brewer-michael/brwr-trmnl/firmware/src/display.cpp

#include <Arduino.h>
#include <display.h>
#include <power.h>
#include <PNGdec.h>
#include <JPEGDEC.h>
#include <Preferences.h>
#include <preferences_persistence.h>
#include <refresh_interval.h>
#include "battery_small.h"
#include "battery_hollow.h"
#include "messages.h"
#include "config.h"
#include "battery.h"
#ifdef BOARD_BRWR_TRMNL
#include <brwr/brwr.h>
#endif
#define MAX_BIT_DEPTH 8
TRMNL_DEVICE *pDevice = NULL;
#ifdef PARALLEL_EPD
#include "FastEPD.h"
FASTEPD bbep;
#else
#define BB_EPAPER
#include <bb_epaper.h>
BBEPAPER bbep;
#ifndef DEVICE_MODEL
#error "Must have a device model name defined in platformio.ini!"
#endif // DEVICE_MODEL
#include <SPIFFS.h>
#define FS SPIFFS
#endif // !PARALLEL_EPD

// List of supported TRMNL devices with SPI ePaper displays. The list can be in any order since the name is matched
// The final parameter is the panel type which is from an enumerated list
#ifdef PARALLEL_EPD
const TRMNL_DEVICE device_list[] = 
{
// name           board_name            panel_type.            sda    scl    intr   batt  batt_en batt_type
  "x",            BB_PANEL_TRMNL_X,     BB_PANEL_NONE,         0xff,  0xff,  0xff,  0xff, 0xff,   BATT_ADC,
  "m5_papers3",   BB_PANEL_M5PAPERS3,   BB_PANEL_NONE,         0xff,  0xff,  0xff,  3,    0xff,   BATT_ADC,
  "sensoria_c5",  BB_PANEL_SENSORIA_C5, BB_PANEL_NONE,         7,     6,     0,     0xff, 0xff,   BATT_ADC,
  "lilygo_t5pro", BB_PANEL_EPDIY_V7,    BBEP_DISPLAY_ED047TC1, 39,    40,    0,     0xff, 0xff,   BATT_BQ27220,
  "brwr_trmnl",   BB_PANEL_IT8951,      BBEP_DISPLAY_ED103TC2, 0xff,  0xff,  2,     PIN_BATTERY, 0xff, BATT_ADC,
  NULL, 0, 0, 0, 0, 0, 0, 0, 0,
}; // Parallel Eink device list

#else // BB_EPAPER boards
const TRMNL_DEVICE device_list[] = 
{
// name            sck   mosi   cs   rst   dc   busy  sda   scl   intr   batt  batt_en, batt_type, panel
  "og",            7,    8,     6,   10,   5,   4,    21,   20,   2,     3,    0xff,    BATT_ADC,  EPD_75,
  "og_4clr",       7,    8,     6,   10,   5,   4,    21,   20,   2,     3,    0xff,    BATT_ADC,  EPD_75_4CLR,
  "og_gen2",       6,    1,     4,   2,    5,   0,    23,   10,   3,     0xff, 0xff,    BATT_BQ27427,  EPD_75, // fake battery == 0xff
  "og_gen2_4clr",  6,    1,     4,   2,    5,   0,    11,   12,   3,     0xff, 0xff,    BATT_BQ27427,  EPD_75_4CLR, // fake battery == 0xff
  "xteink_x4",     8,    10,    21,  5,    4,   6,    0xff, 0xff, 3,     0xff, 0xff,    BATT_ADC,  EPD_426,
  "xteink_x3",     8,    10,    21,  5,    4,   6,    20,   0,    3,     0xff, 0xff,    BATT_BQ27220,  EPD_368,
  "waveshare",     13,   14,    15,  26,   27,  25,   0xff, 0xff, 33,    0xff, 0xff,    BATT_ADC,  EPD_75,
  "waveshare_397", 11,   12,    10,  46,   9,   3,    41,   42,   0,     0xff, 0xff,    BATT_AXP2101,  EPD_397,
  "seeed_sticky",  13,   14,    15,  17,   16,  18,   1,    0,    4,     0xff, 0xff,    BATT_BQ27220,  EPD_397,  
  "seeed_esp32c3", 8,    10,    3,   2,    5,   4,    0xff, 0xff, 9,     0xff, 0xff,    BATT_ADC,  EPD_75,
  "seeed_esp32s3", 7,    9,     2,   1,    4,   3,    0xff, 0xff, 0,     0xff, 0xff,    BATT_ADC,  EPD_75,
  "xiao_epaper_mini", 7, 9,     44,  38,   10,  4,    0xff, 0xff, 2,     1,    6,       BATT_ADC,  EPD_426,
  "xiao_epaper_display", 7, 9,  44,  38,   10,  4,    0xff, 0xff, 5,     1,    6,       BATT_ADC,  EPD_75,
  "xiao_epaper_3clr", 7, 9,     44,  38,   10,  4,    0xff, 0xff, 5,     1,    6,       BATT_ADC,  EPD_75_3CLR,
  "xiao_epaper_6clr", 7, 9,     44,  38,   10,  4,    0xff, 0xff, 5,     1,    6,       BATT_ADC,  EPD_75_6CLR,
  "reterminal_e1001", 7, 9,     10,  12,   11,  13,   0xff, 0xff, 3,     1,    21,      BATT_ADC,  EPD_75,
  "reterminal_e1002", 7, 9,     10,  12,   11,  13,   0xff, 0xff, 3,     1,    21,      BATT_ADC,  EPD_75_6CLR,
  "crowpanel42",   0,    0,     0,   0,    0,   0,    0xff, 0xff, 2,     0xff, 0xff,    BATT_NONE, EPD_CROWPANEL, 
#ifdef CMD_CS1_CS2
  "m5_paper_mono", 0,    0,     0,   0,    0,   0,    47,   48,   2,     0xff, 0xff,    BATT_NONE, EPD_PAPER_MONO, 
  "m5_paper_color", 0,   0,     0,   0,    0,   0,    3,    2,    1,     0xff, 0xff,    BATT_NONE, EPD_PAPER_COLOR, 
  "reterminal_e1004", 0, 0,     0,   0,    0,   0,    0xff, 0xff, 4,     1,    21,      BATT_ADC,  EPD_133_COLOR,
  "trmnl_steam",   7,    8,     6,   10,   5,   4,    21,   20,   2,     3,    0xff,    BATT_ADC,  EPD_583,
#endif
  NULL,            0,    0,     0,   0,    0,   0,    0,    0,    0,     0,    0,       0,         0,
}; // device_list

// TRMNL SPI ePaper panel types list. The list order is fixed and based on enumerated values
// N.B. ALWAYS ADD NEW PANELS TO THE END OF THE LIST
const DISPLAY_PROFILE dpList[12][3] = { // 1-bit and 2-bit display types for each profile
    {{EP75_800x480, EP75_800x480_4GRAY}, {EP75_800x480_GEN2, EP75_800x480_4GRAY_GEN2}, {EP75_800x480, EP75_800x480_4GRAY_V2}},
    {{EP426_800x480, EP426_800x480_4GRAY}, {EP426_800x480, EP426_800x480_4GRAY}, {EP426_800x480, EP426_800x480_4GRAY}},
    {{EP397_800x480, EP397_800x480_4GRAY}, {EP397_800x480, EP397_800x480_4GRAY}, {EP397_800x480, EP397_800x480_4GRAY}},
    {{EP75R_800x480, EP75R_800x480}, {EP75R_800x480, EP75R_800x480}, {EP75R_800x480, EP75R_800x480}}, 
    {{EP75YR_800x480, EP75YR_800x480}, {EP75YR_800x480, EP75YR_800x480}, {EP75YR_800x480, EP75YR_800x480}}, 
    {{EP73_SPECTRA_800x480, EP73_SPECTRA_800x480}, {EP73_SPECTRA_800x480, EP73_SPECTRA_800x480}, {EP73_SPECTRA_800x480, EP73_SPECTRA_800x480}},
    {{EPD_CROWPANEL42, EPD_CROWPANEL42_4GRAY},{EPD_CROWPANEL42, EPD_CROWPANEL42_4GRAY},{EPD_CROWPANEL42, EPD_CROWPANEL42_4GRAY}},
#ifdef CMD_CS1_CS2
    {{EP583_648x480, EP583_648x480_4GRAY}, {EP583_648x480, EP583_648x480_4GRAY}, {EP583_648x480, EP583_648x480_4GRAY}},
    {{EPD_M5_PAPER_MONO, EPD_M5_PAPER_MONO_4GRAY},{EPD_M5_PAPER_MONO, EPD_M5_PAPER_MONO_4GRAY},{EPD_M5_PAPER_MONO, EPD_M5_PAPER_MONO_4GRAY}},
    {{EPD_M5_PAPER_COLOR, EPD_M5_PAPER_COLOR},{EPD_M5_PAPER_COLOR, EPD_M5_PAPER_COLOR},{EPD_M5_PAPER_COLOR, EPD_M5_PAPER_COLOR}},
    {{EPD_SEEED_E1004, EPD_SEEED_E1004},{EPD_SEEED_E1004, EPD_SEEED_E1004},{EPD_SEEED_E1004, EPD_SEEED_E1004}},
    {{EP368_792x528, EP368_792x528_4GRAY}, {EP368_792x528, EP368_792x528_4GRAY}, {EP368_792x528, EP368_792x528_4GRAY}},
#endif
};
uint8_t u8SpectraPal[512]; // RGB333 mapped to closest Spectra6 color
#endif // !PARALLEL_EPD

#ifdef PARALLEL_EPD
#include "esp_sleep.h"
#include "driver/gpio.h"
#include "driver/rtc_io.h"
#include "LittleFS.h"
#define FS LittleFS

const uint8_t u8_graytable[] = {
/* 0 */  0, 0, 0, 0, 0, 0, 1, 1, 1, 
/* 1 */  0, 0, 1, 1, 1, 2, 2, 1, 1, 
/* 2 */  0, 0, 0, 0, 1, 2, 2, 1, 1,
/* 3 */  1, 1, 2, 2, 1, 1, 1, 1, 2, 
/* 4 */  0, 0, 0, 1, 2, 1, 1, 1, 2, 
/* 5 */  1, 2, 2, 2, 2, 1, 1, 1, 2, 
/* 6 */  0, 0, 1, 1, 2, 2, 1, 1, 2, 
/* 7 */  0, 1, 1, 2, 1, 1, 2, 1, 2, 
/* 8 */  0, 1, 1, 1, 2, 1, 2, 1, 2, 
/* 9 */  0, 1, 1, 1, 1, 2, 2, 1, 2, 
/* 10 */  1, 1, 1, 2, 1, 1, 1, 2, 2, 
/* 11 */  0, 0, 1, 2, 1, 1, 1, 2, 2, 
/* 12 */  0, 0, 0, 1, 2, 1, 1, 2, 2, 
/* 13 */  0, 0, 0, 0, 1, 2, 1, 2, 2, 
/* 14 */  0, 1, 1, 1, 2, 2, 2, 2, 2, 
/* 15 */  0, 0, 0, 0, 0, 0, 0, 0, 2
};
#include "BQ27427.h"
extern BQ27427 lipo; // Use lipo.[] to interact with the library in an Arduino 
#endif

#include "Group5.h"
#include <config.h>
#include "wifi_connect_qr.h"
#include "wifi_failed_qr.h"
#include <ctype.h> //iscntrl()
#include <api-client/display.h>
#include <inttypes.h>
#include <trmnl_log.h>
#include "png_flip.h"
#include "fonts/nicoclean_8.h"
#include "fonts/Inter_18.h"
#include "fonts/Roboto_Black_24.h"
#include <globals.h>
static uint8_t *pDither;

#ifdef BB_EPAPER
static bool display_update_epaper(int refreshMode, bool wait, bool writePlane = false, uint8_t plane = PLANE_0)
{
    if (writePlane) {
        bbep.writePlane(plane);
    }
    if (refreshMode == REFRESH_PARTIAL && !bCanDoPartial) {
        refreshMode = REFRESH_FAST;
        Log_info("Can't do partial refresh, no previous image");
    } else {
        Log_info("Have valid previous image in EPD memory, doing partial refresh");
    }
    bbep.refresh(refreshMode, wait);
    // The next update can be a partial update because the current is 1-bpp and stays in the EPD RAM
    bCanDoPartial = (bbep.getPanelType() == dpList[pDevice->panel_set][iTempProfile].OneBit);
    return true;
}

static void WriteSPIByte(uint8_t data)
{
  for (int i=0; i<8; i++) {
    digitalWrite(pDevice->epd_mosi_pin, (data & 0x80) ? 1:0);
    digitalWrite(pDevice->epd_sck_pin, 1);
    digitalWrite(pDevice->epd_sck_pin, 0);
    data <<= 1;
  }
}

static uint8_t ReadSPIByte(void)
{
uint8_t u8 = 0;
  for (int i=0; i<8; i++) {
    digitalWrite(pDevice->epd_sck_pin, 1);
    digitalWrite(pDevice->epd_sck_pin, 0);
    u8 <<= 1;
    u8 |= digitalRead(pDevice->epd_mosi_pin);
  }
return u8;
}
/**
 * @brief Function to read the EPD revision to know what temperature profile to use
 * @param none
 * @return 32-bit value read from the panel's revision (REV) command
 */
uint32_t get_panel_rev(void)
{
    uint32_t u32 = 0;
    uint8_t u8;

    if (pDevice->epd_mosi_pin == 0 && pDevice->epd_sck_pin == 0) { // pre-defined PCB+display in bb_epaper; pins unknown
        return 0;
    }
    if (pDevice->panel_set != EPD_75) { // REV (0x70) is only known to be a harmless read on the 7.5" B/W UC8179
        return 0;
    }

    // Initialize the SPI bus in 'bit-bang' mode before running the normal init sequence
    // This will allow us to use MOSI as a bidirectional line for reading data from the panel
    pinMode(pDevice->epd_sck_pin, OUTPUT);
    pinMode(pDevice->epd_cs_pin, OUTPUT);
    digitalWrite(pDevice->epd_cs_pin, 1);
    pinMode(pDevice->epd_rst_pin, OUTPUT);
    pinMode(pDevice->epd_dc_pin, OUTPUT);
    pinMode(pDevice->epd_busy_pin, INPUT);

    // Reset the panel
    digitalWrite(pDevice->epd_rst_pin, 0);
    delay(20);
    digitalWrite(pDevice->epd_rst_pin, 1);
    delay(20);
    if (digitalRead(pDevice->epd_busy_pin) == 0) { // it's a SSD16xx; not useful at the moment because our 7.5" B/W is a UC81xx type panel
        return 0;
    }
    digitalWrite(pDevice->epd_dc_pin, 0); // command mode
    digitalWrite(pDevice->epd_cs_pin, 0);
    pinMode(pDevice->epd_mosi_pin, OUTPUT);
    WriteSPIByte(0x70); // Revision (REV) command
    digitalWrite(pDevice->epd_dc_pin, 1); // data mode
    pinMode(pDevice->epd_mosi_pin, INPUT);
    for (int i=0; i<7; i++) {
        u8 = ReadSPIByte();
        if (i >= 3) { // first 3 bytes are 0xff
            u32 <<= 8;
            u32 |= u8;
        }
    }
    digitalWrite(pDevice->epd_cs_pin, 1);
    return u32;
} /* get_panel_rev() */
#endif // BB_EPAPER

String display_panel_rev_string(void)
{
    if (panel_rev == 0) {
        return String();
    }
    char sz[9];
    snprintf(sz, sizeof(sz), "%08" PRIx32, panel_rev);
    return String(sz);
} /* display_panel_rev_string() */

void hw_config_init(void)
{
    int i = 0;
    // Match the device name with the configuration in the list
    while (device_list[i].device_name && strcmp(device_list[i].device_name, DEVICE_MODEL) != 0) {
        i++;
    }
    if (device_list[i].device_name) {
        Log_info("Found device model at index %d\n", i);
        pDevice = (TRMNL_DEVICE *)&device_list[i];
    } else {
        Log_info("Device name (%s) not found in supported list!", device_list[i].device_name);
    }
} /* hw_config_init() */

/**
 * @brief Function to init the display
 * @param none
 * @return none
 */
void display_init(void)
{
    if (pDevice == NULL) {
        hw_config_init();
    }
    Log_info("dev module start");
    iTempProfile = preferences.getUInt(PREFERENCES_TEMP_PROFILE, TEMP_PROFILE_DEFAULT);
    Log_info("Saved temperature profile: %" PRIu32, iTempProfile);
#ifdef BB_EPAPER
    Log_info("BB e-Paper init");
#ifdef BOARD_SEEED_STICKY
// Special case for the Sticky - it shares the SPI bus with the uSD card, so the EPD CS line
// must be the only one active at a time
    pinMode(8, OUTPUT); // SD card CS (shared SPI with EPD)
    digitalWrite(8, 1); // SD CS disabled
    pinMode(47, OUTPUT);
    digitalWrite(47, 1); // enable EPD power
    pinMode(10, OUTPUT); // SD card enable (if it's powered down, the SPI bus may be blocked)
    digitalWrite(10, 1);
#endif // BOARD_SEEED_STICKY
    // Read the panel ID after any board-specific power/CS setup, but before bb_epaper takes over the SPI pins
    panel_rev = get_panel_rev();
    Log_info("Panel ID = 0x%08x\n", panel_rev);
    if (pDevice->epd_mosi_pin != 0 || pDevice->epd_sck_pin != 0) {
        bbep.setPanelType(dpList[pDevice->panel_set][iTempProfile].OneBit); // must be set BEFORE calling initio
        bbep.initIO(pDevice->epd_dc_pin, pDevice->epd_rst_pin, pDevice->epd_busy_pin, pDevice->epd_cs_pin,
        pDevice->epd_mosi_pin, pDevice->epd_sck_pin, 8000000);
    } else { // it's a pre-defined PCB+display in bb_epaper
        bbep.begin(dpList[pDevice->panel_set][0].OneBit);
    }
#else // Parallel eink devices
#if defined (BOARD_SEEED_RETERMINAL_E1003) || defined(BOARD_BRWR_TRMNL)
    bbep.initIT8951(EPD_MOSI_PIN, EPD_MISO_PIN, EPD_SCK_PIN, EPD_CS_PIN, EPD_BUSY_PIN, EPD_RST_PIN, EPD_EN_PIN, EPD_VCC_EN);
    bbep.setPanelSize(BBEP_DISPLAY_ED103TC2);
#ifdef BOARD_BRWR_TRMNL
    brwr::panel_after_init(); // this panel's VCOM, SPI clock for hand wiring
#endif
#else // normal parallel eink devices
    bbep.initPanel(pDevice->iBoardType);
    if (pDevice->iPanelSize != BB_PANEL_NONE) {
        bbep.setPanelSize(pDevice->iPanelSize);
    }
#endif
#ifdef BOARD_TRMNL_X
//    bbep.initPanel(BB_PANEL_TRMNL_X);
    bbep.setPasses(3, 3); // The 10.3" panel needs fewer pushes
#endif
//#elif defined( BOARD_TRMNL_X_SENSORIAS3 )
//    bbep.initPanel(BB_PANEL_V7_RAW);
//    bbep.setPanelSize(1280, 720, BB_PANEL_FLAG_MIRROR_X, -1600);
//#elif defined( BOARD_TRMNL_X_SENSORIAC5 )
//    bbep.initPanel(BB_PANEL_SENSORIA_C5);
//#elif defined(BOARD_TRMNL_X_PAPERS3)
//    bbep.initPanel(BB_PANEL_M5PAPERS3);
//#elif defined(BOARD_TRMNL_X_LILYGO)
//    bbep.initPanel(BB_PANEL_EPDIY_V7);
//    bbep.setPanelSize(960, 540);
#endif // bb_epaper
    Log_info("dev module end");
}

#ifdef BOARD_TRMNL_X

#define TCA9535_INT 38

void BQ27427_reset()
{
    bbep.ioPinMode(10, OUTPUT);

    bbep.ioWrite(10, LOW);
    delay(10);

    bbep.ioWrite(10, HIGH);
    Serial.println("BQ27427 reset performed");
}

void config_tca95535_pins_for_lp()
{
    bbep.ioPinMode(0, INPUT);

    // Pin 1 (OTG) is configured separately in init_otg()

    bbep.ioPinMode(2, INPUT);

    bbep.ioPinMode(3, INPUT);

    bbep.ioPinMode(4, INPUT);

    bbep.ioPinMode(5, INPUT);

    bbep.ioPinMode(6, OUTPUT);
    bbep.ioWrite(6, LOW);

    bbep.ioPinMode(7, INPUT);

    bbep.ioPinMode(8, OUTPUT);
    bbep.ioWrite(8, LOW);

    bbep.ioPinMode(9, OUTPUT);
    bbep.ioWrite(9, LOW);

    bbep.ioPinMode(10, INPUT);

    bbep.ioPinMode(11, OUTPUT);
    bbep.ioWrite(11, LOW);

    bbep.ioPinMode(12, OUTPUT);
    bbep.ioWrite(12, LOW);

    bbep.ioPinMode(13, OUTPUT);
    bbep.ioWrite(13, LOW);

    bbep.ioPinMode(14, INPUT);

    bbep.ioPinMode(15, INPUT);
}

void config_bma530_interrupt()
{
    bbep.ioPinMode(3, INPUT);
    bbep.ioRead(10);
}

uint8_t tca9535_interrupt_clear()
{
    return bbep.ioRead(3);
}

void otg_turn_on()
{
    bbep.ioPinMode(1, OUTPUT);
    bbep.ioWrite(1, HIGH);
    Log_info("OTG turned on");
}

void otg_turn_off()
{
    bbep.ioPinMode(1, OUTPUT);
    bbep.ioWrite(1, LOW);
    Log_info("OTG turned off");
}

#define BAT_DET_PIN       7    // TCA9535 P0_7 in bbep pin numbering
#define BAT_CHARGE_MS     2    // drive HIGH for 2 ms to charge RC network
#define BAT_TIMEOUT_US    6000 // no battery if pin is still HIGH after this
#define BAT_THRESHOLD_US  750 // >750 µs → 1 cell; ≤750 µs → 2 cells

static battery_count_t measure_battery_once()
{
    // -- Charge RC network: drive P0_7 HIGH for 2 ms --
    bbep.ioPinMode(BAT_DET_PIN, OUTPUT);
    bbep.ioWrite(BAT_DET_PIN, HIGH);
    delay(BAT_CHARGE_MS);

    // -- Release: switch to input and start timing --
    bbep.ioPinMode(BAT_DET_PIN, INPUT);

    unsigned long start = micros();
    unsigned long now   = start;
    bool timeout = false;

    while (true) {
        bool still_high = (bbep.ioRead(BAT_DET_PIN) != 0);
        now = micros();

        if (!still_high) break;               // pin went LOW → discharged

        if ((now - start) >= BAT_TIMEOUT_US) {
            timeout = true;
            break;
        }
    }

    if (timeout)                         return BATTERY_NONE;
    if ((now - start) > BAT_THRESHOLD_US) return BATTERY_ONE;
    return BATTERY_TWO;
}

battery_count_t detect_battery_count()
{
    battery_count_t last = (battery_count_t)-1;

    for (int attempt = 0; attempt < 20; attempt++) {
        battery_count_t result = measure_battery_once();

        if (result == last) {
            // Two identical results in a row — confident reading
            Log_info("Battery detection: %s (confirmed after %d attempt(s))",
                result == BATTERY_NONE ? "none" :
                result == BATTERY_ONE  ? "1 cell" : "2 cells",
                attempt + 1);
            return result;
        }

        last = result;
        delay(10);
    }

    // Fallback: return last reading if we never got two in a row
    Log_error("Battery detection: unstable reading — defaulting to last result");
    return last;
}

void enter_shipment_sleep()
{
    config_tca95535_pins_for_lp();
    bbep.ioPinMode(0, INPUT);  // Pin 0 = charger detect

    // Clear any pending TCA9535 interrupts
    for (uint8_t pin = 0; pin < 16; pin++) {
        bbep.ioPinMode(pin, INPUT);
        bbep.ioRead(pin);
    }
    delay(50);

    pinMode(TCA9535_INT, INPUT_PULLUP);

    // Check initial GPIO38 state
    int gpio38_state = digitalRead(TCA9535_INT);

    // Enable GPIO wakeup for light sleep
    esp_err_t err = esp_sleep_enable_gpio_wakeup();
    if (err != ESP_OK) {
        Serial.printf("ERROR: Failed to enable GPIO wakeup: %d\n", err);
        return;
    }

    err = gpio_wakeup_enable((gpio_num_t)TCA9535_INT, GPIO_INTR_LOW_LEVEL);
    if (err != ESP_OK) {
        Serial.printf("ERROR: Failed to configure GPIO38 wakeup: %d\n", err);
        return;
    }

    Serial.println("=== Entering shipment mode light sleep loop ===");
    delay(100);

    uint32_t sleep_count = 0;

    // Main sleep loop
    while (true) {
        sleep_count++;

        esp_light_sleep_start();

        // Re-initialize Serial after light sleep (USB may have been disabled)
        delay(100);
        Serial.begin(115200);
        delay(100);

        Serial.println("\n=== WAKEUP from light sleep ===");
        Serial.printf("Sleep cycle: %lu\n", sleep_count);

        // Check wakeup cause
        esp_sleep_wakeup_cause_t wakeup_reason = esp_sleep_get_wakeup_cause();
        Serial.printf("Wakeup cause: %d (GPIO=%d)\n", wakeup_reason, ESP_SLEEP_WAKEUP_GPIO);

        if (wakeup_reason == ESP_SLEEP_WAKEUP_GPIO) {
            Serial.println("GPIO wakeup detected");

            // Check GPIO38 state
            gpio38_state = digitalRead(TCA9535_INT);
            Serial.printf("GPIO38 state after wakeup: %d\n", gpio38_state);

            // Check if charger connected (TCA9535 pin 0 LOW)
            bbep.ioPinMode(0, INPUT);
            delay(10);
            uint8_t pin0_state = bbep.ioRead(0);
            Serial.printf("TCA9535 pin 0 (charger detect): %d (0=charger present)\n", pin0_state);

            if (pin0_state == 0) {
                Serial.println("*** CHARGER DETECTED - Exiting shipment mode ***");
                Serial.flush();
                delay(100);
                break;  // Exit shipment mode
            }

            // False wakeup - clear interrupt and continue
            for (uint8_t pin = 0; pin < 16; pin++) {
                bbep.ioPinMode(pin, INPUT);
                bbep.ioRead(pin);
            }
            delay(50);

            gpio38_state = digitalRead(TCA9535_INT);
            Serial.printf("GPIO38 after clear: %d\n", gpio38_state);

        } else {
            Serial.printf("Unexpected wakeup cause: %d\n", wakeup_reason);
        }

        Serial.println("Returning to sleep...\n");
        Serial.flush();
        delay(100);
    }

    gpio_wakeup_disable((gpio_num_t)TCA9535_INT);
    gpio_set_intr_type((gpio_num_t)TCA9535_INT, GPIO_INTR_DISABLE);
    Serial.println("=== Exited shipment mode successfully ===");
    Serial.flush();
}

#define PIN_ESP32C5_SPI_BOOT 4
#define PIN_ESP32C5_USB_BOOT 5
#define PIN_ESP32C5_EN 6

void modem_enter_bootloader(void) {
  // Disable target and wait for full power down
  bbep.ioWrite(PIN_ESP32C5_EN, 0);
  delay(100);

  // Configure boot pins for bootloader mode
  bbep.ioPinMode(PIN_ESP32C5_SPI_BOOT, OUTPUT);
  bbep.ioPinMode(PIN_ESP32C5_USB_BOOT, OUTPUT);
  bbep.ioWrite(PIN_ESP32C5_SPI_BOOT, 0);
  bbep.ioWrite(PIN_ESP32C5_USB_BOOT, 1);
  delay(50);

  // Enable target in bootloader mode
  bbep.ioWrite(PIN_ESP32C5_EN, 1);
  delay(300);
}

void modem_reset_target(void) {
  // Disable target
  bbep.ioWrite(PIN_ESP32C5_EN, 0);
  delay(50);

  // Release boot pins (set to input for normal boot)
  bbep.ioPinMode(PIN_ESP32C5_SPI_BOOT, INPUT);
  bbep.ioPinMode(PIN_ESP32C5_USB_BOOT, INPUT);
  delay(50);

  // Enable target (normal boot)
  bbep.ioWrite(PIN_ESP32C5_EN, 1);
}

#endif

/**
 * @brief Enable or disable light sleep at runtime
 * @param enabled true to enable light sleep, false to disable
 * @return none
 */
void display_set_light_sleep(uint8_t enabled)
{
#ifdef BB_EPAPER
    bbep.setLightSleep(enabled);
#endif
}

// Clear any ghosting on the X display by wiping it black/white many times
void display_wipe(void)
{
#ifdef BB_EPAPER

#ifdef BOARD_TRMNL_4CLR
    int refreshCount = 2;
#else
    int refreshCount = 60;
#endif

    bbep.setPanelType(dpList[pDevice->panel_set][iTempProfile].OneBit);
    bbep.fillScreen(BBEP_WHITE);
    for (int i=0; i<refreshCount; i++) {
        bbep.refresh(REFRESH_FULL); // 2 to 3 minutes of Black/White clearing of the display
    }
    bbep.sleep(LIGHT_SLEEP);
#else
    bbep.setMode(BB_MODE_1BPP);
    bbep.fillScreen(BBEP_WHITE);
    for (int i=0; i<100; i++) { // 200 black/white cycles should remove any ghosting
        bbep.fullUpdate(CLEAR_SLOW, true);
    }
    bbep.einkPower(0); // power off the display
#endif
} /* display_wipe() */

/**
 * @brief Function to sleep the ESP32 while saving power
 * @param u32Millis represents the sleep time in milliseconds
 * @return none
 */
void display_sleep(uint32_t u32Millis)
{
#ifdef DO_NOT_LIGHT_SLEEP
    delay(u32Millis);
#else
    // Runtime control for light sleep (true = enabled, false = disabled)
    static bool light_sleep_enabled = true;
    if (!light_sleep_enabled) {
        delay(u32Millis);
    } else {
        esp_sleep_enable_timer_wakeup(u32Millis * 1000L);
        esp_light_sleep_start();
    }
#endif
}

/**
 * @brief Function to reset the display
 * @param none
 * @return none
 */
void display_reset(void)
{
    Log_info("e-Paper Clear start");
    bbep.fillScreen(BBEP_WHITE);
#ifdef BB_EPAPER
#ifndef BOARD_SEEED_RETERMINAL_E1002
    bbep.setLightSleep(true);
#endif
    if (!display_update_epaper(apiDisplayResult.response.maximum_compatibility ? REFRESH_FULL : REFRESH_FAST, true)) {
        Log_error("display_reset: e-paper update failed");
    }
#else
    bbep.fullUpdate();
#endif
    Log_info("e-Paper Clear end");
    // DEV_Delay_ms(500);
}

/**
 * @brief Function to read the display height
 * @return uint16_t - height of display in pixels
 */
uint16_t display_height()
{
    return bbep.height();
}

/**
 * @brief Function to read the display width
 * @return uint16_t - width of display in pixels
 */
uint16_t display_width()
{
    return bbep.width();
}

#ifdef PARALLEL_EPD
void display_draw_touchbar_indicator(touchbar_side_t side, bool filled)
{
    const int radius = 24;
    const int margin_bottom = 20;
    int w = bbep.width();
    int h = bbep.height();
    int x;
    Log_info("Drawing touchbar indicator %d\n", (int)side);
    switch (side) {
        case TOUCHBAR_LEFT:   x = w / 6;     break;
        case TOUCHBAR_MIDDLE: x = w / 2;     break;
        case TOUCHBAR_RIGHT:  x = w * 5 / 6; break;
        default: return;
    }
    int y = h - margin_bottom - radius;
    int prev_mode = bbep.getPreviousMode();
        const int rect_h = radius * 2;
        const int rect_w = rect_h * 4;
        const int border = 3;
        int rx = x - rect_w / 2;
        int ry = y - rect_h / 2;
        uint8_t fill_color   = filled ? BBEP_BLACK : BBEP_WHITE;
        uint8_t border_color = filled ? BBEP_WHITE : BBEP_BLACK;
        if (prev_mode == BB_MODE_NONE) {
            bbep.setMode(BB_MODE_1BPP);
            // No previous image, so in order to get what we need in a partial update, we need to
            // set the colors to the opposite of what we want drawn.
            bbep.fillScreen(BBEP_WHITE);
            bbep.drawRect(rx - border - 1, ry - border - 1, rect_w + 2 + (2*border), rect_h + 2 + (2*border), border_color);
            bbep.fillRect(rx - border, ry - border, rect_w + (2*border), rect_h + (2*border), fill_color);
            bbep.fillRect(rx, ry, rect_w, rect_h, border_color);
            int sz = bbep.width() * bbep.height() / 8; // 1-bit per pixel
            memcpy(bbep.previousBuffer(), bbep.currentBuffer(), sz);
            bbep.setPreviousMode(BB_MODE_1BPP);
        }
        // Draw outline, then larger filled rect for border color and inner for fill color
        bbep.drawRect(rx - border - 1, ry - border - 1, rect_w + 2 + (2*border), rect_h + 2 + (2*border), fill_color);
        bbep.fillRect(rx - border, ry - border, rect_w + (2*border), rect_h + (2*border), border_color);
        bbep.fillRect(rx, ry, rect_w, rect_h, fill_color);
        bbep.partialUpdate(false);
} /* display_draw_touchbar_indicator() */
#endif

/**
 * @brief Function to draw multi-line text onto the display
 * @param x_start X coordinate to start drawing
 * @param y_start Y coordinate to start drawing
 * @param message Text message to draw
 * @param max_width Maximum width in pixels for each line
 * @param font_width Width of a single character in pixels
 * @param color_fg Foreground color
 * @param color_bg Background color
 * @param font Font to use
 * @param is_center_aligned If true, center the text; if false, left-align
 * @return none
 */
void Paint_DrawMultilineText(UWORD x_start, UWORD y_start, const char *message,
                             uint16_t max_width, uint16_t font_width,
                             UWORD color_fg, UWORD color_bg, const void *font,
                             bool is_center_aligned)
{
    BB_FONT_SMALL *pFont = (BB_FONT_SMALL *)font;
    uint16_t display_width_pixels = max_width;
    int max_chars_per_line = display_width_pixels / font_width;
    const int font_height = pFont->height;
    uint8_t MAX_LINES = 4;

    char lines[MAX_LINES][max_chars_per_line + 1] = {0};
    uint16_t line_count = 0;

    int text_len = strlen(message);
    int current_width = 0;
    int line_index = 0;
    int line_pos = 0;
    int word_start = 0;
    int i = 0;
    char word_buffer[max_chars_per_line + 1] = {0};
    int word_length = 0;

    bbep.setFont(font);
    bbep.setTextColor(color_fg, color_bg);

    bbep.setFont(font);
    bbep.setTextColor(color_fg, color_bg);

    while (i <= text_len && line_index < MAX_LINES)
    {
        word_length = 0;
        word_start = i;

        // Skip leading spaces
        while (i < text_len && message[i] == ' ')
        {
            i++;
        }
        word_start = i;

        // Find end of word or end of text
        while (i < text_len && message[i] != ' ')
        {
            i++;
        }

        word_length = i - word_start;
        if (word_length > max_chars_per_line)
        {
            word_length = max_chars_per_line; // Truncate if word is too long
        }

        if (word_length > 0)
        {
            strncpy(word_buffer, message + word_start, word_length);
            word_buffer[word_length] = '\0';
        }
        else
        {
            i++;
            continue;
        }

        int word_width = word_length * font_width;

        // Check if adding the word exceeds max_width
        if (current_width + word_width + (current_width > 0 ? font_width : 0) <= display_width_pixels)
        {
            // Add space before word if not the first word in the line
            if (current_width > 0 && line_pos < max_chars_per_line - 1)
            {
                lines[line_index][line_pos++] = ' ';
                current_width += font_width;
            }

            // Add word to current line
            if (line_pos + word_length <= max_chars_per_line)
            {
                strcpy(&lines[line_index][line_pos], word_buffer);
                line_pos += word_length;
                current_width += word_width;
            }
        }
        else
        {
            // Current line is full, draw it
            if (line_pos > 0)
            {
                lines[line_index][line_pos] = '\0'; // Null-terminate the current line
                line_index++;
                line_count++;

                if (line_index >= MAX_LINES)
                {
                    break;
                }

                // Start new line with this word
                strncpy(lines[line_index], word_buffer, word_length);
                line_pos = word_length;
                current_width = word_width;
            }
            else
            {
                // Single long word case
                strncpy(lines[line_index], word_buffer, max_chars_per_line);
                lines[line_index][max_chars_per_line] = '\0';
                line_index++;
                line_count++;
                line_pos = 0;
                current_width = 0;
            }
        }

        // Move to next word
        if (message[i] == ' ')
        {
            i++;
        }
    }

    // Store the last line if any
    if (line_pos > 0 && line_index < MAX_LINES)
    {
        lines[line_index][line_pos] = '\0';
        line_count++;
    }

    // Draw the lines
    for (int j = 0; j < line_count; j++)
    {
        uint16_t line_width = strlen(lines[j]) * font_width;
        uint16_t draw_x = x_start;

        if (is_center_aligned)
        {
            if (line_width < max_width)
            {
                draw_x = x_start + (max_width - line_width) / 2;
            }
        }
        bbep.setCursor(draw_x, y_start + j * (font_height + 5));
        bbep.print(lines[j]);
    }
}
/**
 * @brief Reduce the bit depth of line of pixels using thresholding (aka simple color mapping)
 * @param Destination bit count (1 or 2)
 * @param Pointer to a PNG palette (3 bytes per entry)
 * @param Pointer to the source pixels
 * @param Pointer to the destination pixels
 * @param Pixel count
 * @param Original bit depth
 * @return none
 */
void ReduceBpp(int iDestBpp, int iPixelType, uint8_t *pPalette, uint8_t *pSrc, uint8_t *pDest, int w, int iSrcBpp)
{
    int g = 0, x, iDelta;
    uint8_t *s, *d, *pPal, u8, count;
    const uint8_t u8G2ToG8[4] = {0x00, 0x55, 0xaa, 0xff}; // 2-bit to 8-bit gray

    if (iPixelType == PNG_PIXEL_TRUECOLOR) iSrcBpp = 24;
    else if (iPixelType == PNG_PIXEL_TRUECOLOR_ALPHA) iSrcBpp = 32;
    iDelta = iSrcBpp/8; // bytes per pixel
    count = 8; // bits in a byte
    u8 = 0; // start with all black
    d = pDest;
    s = pSrc;
    for (x=0; x<w; x++) {
        u8 <<= iDestBpp;
        switch (iSrcBpp) {
            case 24:
            case 32:
                g = (s[0] + s[1]*2 + s[2])/4; // convert color to gray value
                s += iDelta;
                break;
            case 8:
                if (iPixelType == PNG_PIXEL_INDEXED) {
                    pPal = &pPalette[s[0] * 3];
                    g = (pPal[0] + pPal[1]*2 + pPal[2])/4;
                } else { // must be grayscale
                    g = s[0];
                }
                s++;
                break;
            case 4:
                if (x & 1) {
                    if (iPixelType == PNG_PIXEL_INDEXED) {
                        pPal = &pPalette[(s[0] & 0xf) * 3];
                        g = (pPal[0] + pPal[1]*2 + pPal[2])/4;
                    } else {
                        g = (s[0] & 0xf) | (s[0] << 4);
                    }
                    s++;
                } else {
                    if (iPixelType == PNG_PIXEL_INDEXED) {
                        pPal = &pPalette[(s[0]>>4) * 3];
                        g = (pPal[0] + pPal[1]*2 + pPal[2])/4;
                    } else {
                        g = (s[0] & 0xf0) | (s[0] >> 4);
                    }
                }
                break;
            case 2: // We need to handle this case for 2-bit images with (random) palettes
                g = s[0] >> (6-((x & 3) * 2));
                if (iPixelType == PNG_PIXEL_INDEXED) {
                    pPal = &pPalette[(g & 3)*3];
                    g = (pPal[0] + pPal[1]*2 + pPal[2])/4;
                } else {
                    g = u8G2ToG8[g & 3];
                }
                if ((x & 3) == 3) {
                    s++;
                }
                break;
        } // switch on bpp
        if (iDestBpp == 1) {
            u8 |= (g >> 7); // B/W
        } else if (iDestBpp == 2) { // generate 4 gray levels (2 bits)
            u8 |= (3 ^ (g >> 6)); // 4 gray levels (inverted relative to 1-bit)
        } else { // must be 4-bpp output
            u8 |= (g >> 4);
        }
        count -= iDestBpp;
        if (count == 0) { // byte is full, move on
            *d++ = u8;
            u8 = 0;
            count = 8;
        }
    } // for x
    if (count != 8) { // partial byte remaining
        u8 <<= count;
        *d++ = u8;
    }
} /* ReduceBpp() */
enum {
    PNG_1_BIT = 0,
    PNG_1_BIT_INVERTED,
    PNG_2_BIT_0,
    PNG_2_BIT_1,
    PNG_2_BIT_BOTH,
    PNG_2_BIT_INVERTED,
};
#ifdef BB_EPAPER
//
// Match the given pixel to black (00), white (01), or red (1x)
//
unsigned char GetBWRPixel(int r, int g, int b)
{
    uint8_t ucOut=BBEP_BLACK;
    int gr;

    gr = (b + r + g*2)>>2; // gray
    // match the color to closest of black/white/red
    if (r > g && r > b) { // red is dominant
        if (gr < 100 && r < 80) {
            // black
        } else {
            if (r-b > 32 && r-g > 32) {
                // is red really dominant?
                ucOut = BBEP_RED; // red (can be 2 or 3, but 3 is compatible w/BWYR)
            } else { // yellowish should be white
                // no, use white instead of pink/yellow
                ucOut = BBEP_WHITE;
            }
        }
    } else { // check for white/black
        if (gr >= 128) {
            ucOut = BBEP_WHITE; // white
        } else {
            // black
        }
    }
    return ucOut;
} /* GetBWRPixel() */
//
// Match the given pixel to black (00), white (01), yellow (10), or red (11)
// returns 2 bit value of closest matching color
//
unsigned char GetBWYRPixel(int r, int g, int b)
{
    uint8_t ucOut=BBEP_BLACK;
    int gr;

    gr = (b + r + g*2)>>2; // gray
    // match the color to closest of black/white/yellow/red
    if (r > b || g > b) { // red or yellow is dominant
        if (gr < 90 && r < 80 && g < 80) {
            // black
        } else {
            if (r-b > 32 && r-g > r/2) {
                // is red really dominant?
                ucOut = BBEP_RED; // red
            } else if (r-b > 32 && g-b > 32) {
                // yes, yellow
                ucOut = BBEP_YELLOW;
            } else {
                ucOut = BBEP_WHITE; // gray/white
            }
        }
    } else { // check for white/black
        if (gr >= 100) {
            ucOut = BBEP_WHITE; // white
        } else {
            // black
        }
    }
    return ucOut;
} /* GetBWYRPixel() */

//
// bb_epaper colors to map to Spectra6 colors
// The RGB values are not correct for the panel, but for simple mapping
// these work best. These get mapped from bb_epaper color indices to
// Spectra6 color indices by the setPixel() method.
//
const int iSpectraRGB[] = { // r, g, b
    0, 0, 0, // black = 0
    192,192,192, // white = 1
    192,192,0, // yellow = 2
    192,0,0, // red = 3
    0,0,192, // blue = 4
    0,192,0, // green = 5
};
// Map the Spectra6 palette to the closest RGB333 values
void CreateSpectra6Pal(void)
{
    int i, j;
    int r, g, b, r1, g1, b1;
    int dist, min_dist, min_index;

    for (i=0; i<512; i++) { // RGB333
        r = (i & 7)*36;
        g = ((i >> 3) & 7)*36;
        b = (i >> 6)*36;
        min_dist = 0x7fffffff;
        min_index = 0;
        for (j=0; j<6; j++) { // match to the closes Spectra6 color
            r1 = iSpectraRGB[j*3];
            g1 = iSpectraRGB[j*3+1];
            b1 = iSpectraRGB[j*3+2];
            dist = (r - r1) * (r - r1); // delta red squared
            dist += (g - g1) * (g - g1); // delta green squared
            dist += (b - b1) * (b - b1); // delta blue squared
            if (dist < min_dist) {
                min_dist = dist;
                min_index = j;
            }
        } // for j
        u8SpectraPal[i] = min_index; // best match palette index for this RGB333 color
    } // for i
} /* CreateSpectra6Pal() */
//
// Convert the RGB value into one of 6 Spectra6 colors
//
uint8_t GetSpectraPixel(int r, int g, int b)
{
uint8_t c;
uint16_t rgb333;

    rgb333 = (r>>5) + ((g & 0xe0) >> 2) + ((b & 0xe0) << 1);
    c = u8SpectraPal[rgb333];
    return c;
} /* GetSpectraPixel() */

/**
 * @brief Callback function for each line of PNG decoded
 * @param PNGDRAW structure containing the current line and relevant info
 * @return none
 */
//
// Draw the PNG image into the local framebuffer memory using the drawPixel() method
// to do color translation and to properly format the memory layout
//
int png_draw_6clr(PNGDRAW *pDraw)
{
    uint8_t r=0, g=0, b=0, *s, *pPal, *pPalette = pDraw->pPalette;
    int x, y, iDelta, iBpp = pDraw->iBpp;
    y = pDraw->y;
    switch (pDraw->iPixelType) {
        case PNG_PIXEL_INDEXED:
            break;
        case PNG_PIXEL_TRUECOLOR:
	        if (iBpp <= 8) {
                iBpp *= 3;
	        }
            pPalette = NULL;
            break;
        case PNG_PIXEL_TRUECOLOR_ALPHA:
	        if (iBpp <= 8) {
                iBpp *= 4;
	        }
            pPalette = NULL;
            break;
        case PNG_PIXEL_GRAYSCALE:
            pPalette = NULL;
            break;
    } // switch on pixel type
    iDelta = iBpp/8;
    s = pDraw->pPixels;
    for (x=0; x<pDraw->iWidth; x++) { // slower code, but less code :)
        switch (iBpp) {
            case 24:
            case 32:
                r = s[0];
                g = s[1];
                b = s[2];
                s += iDelta;
                break;
            case 16:
                r = s[1] & 0xf8; // red
                g = ((s[0] | s[1] << 8) >> 3) & 0xfc; // green
                b = s[0] << 3;
                s += 2;
                break;
                case 8:
                    if (pPalette) {
                        pPal = &pPalette[s[0] * 3];
                        r = pPal[0];
                        g = pPal[1];
                        b = pPal[2];
                    } else {
                        r = g = b = s[0];
                    }
                    s++;
                    break;
                case 4:
                    if (pPalette) {
                        if (x & 1) {
                            pPal = &pPalette[(s[0] & 0xf) * 3];
                            s++;
                        } else {
                            pPal = &pPalette[(s[0]>>4) * 3];
                        }
                        r = pPal[0];
                        g = pPal[1];
                        b = pPal[2];
                    } else {
                        if (x & 1) {
                            r = g = b = (s[0] & 0xf) | (s[0] << 4);
                            s++;
                        } else {
                            r = g = b = (s[0] >> 4) | (s[0] & 0xf0);
                        }
                    }
                    break;
		case 2:
		    if (pPalette) {
			pPal = &pPalette[((s[0] >> ((3-(x&3))*2)) & 3) * 3];
			r = pPal[0]; g = pPal[1]; b = pPal[2];
		    } else {
			r = g = b = (s[0] << ((x&3)*2)) & 0xc0;
		    }
		    if ((x & 3) == 3) s++;
		    break;
                case 1:
                    if (pPalette) {
                        pPal = &pPalette[((s[0] >> (7-(x&7))) & 1) * 3];
                        r = pPal[0]; g = pPal[1]; b = pPal[2];
                    } else {
                        r = g = b = ((s[0] << (x&7)) & 0x80);
                    }
                    if ((x & 7) == 7) s++;
                    break;
            } // switch on bpp
            bbep.drawPixel(x, y, GetSpectraPixel(r, g, b));
        } // for x
    return 1; // continue decoding
} /* png_draw_6clr() */

#ifdef BOARD_TRMNL_4CLR
//
// Draw the PNG image into the local framebuffer memory using the drawPixel() method
// to do color translation and to properly format the memory layout
//
int png_draw_4clr(PNGDRAW *pDraw)
{
    uint8_t r=0, g=0, b=0, *s, *pPal, *pPalette = pDraw->pPalette;
    int x, iDelta, iBpp = pDraw->iBpp;
    uint8_t uc=0, *d, *pTemp = bbep.getCache(); // get some scratch memory (not from the stack)

    d = pTemp;
    switch (pDraw->iPixelType) {
        case PNG_PIXEL_INDEXED:
            break;
        case PNG_PIXEL_TRUECOLOR:
	        if (iBpp <= 8) {
                iBpp *= 3;
	        }
            pPalette = NULL;
            break;
        case PNG_PIXEL_TRUECOLOR_ALPHA:
	        if (iBpp <= 8) {
                iBpp *= 4;
	        }
            pPalette = NULL;
            break;
        case PNG_PIXEL_GRAYSCALE:
            pPalette = NULL;
            break;
    } // switch on pixel type
    iDelta = iBpp/8;
    s = pDraw->pPixels;
    for (x=0; x<pDraw->iWidth; x++) { // slower code, but less code :)
        switch (iBpp) {
            case 24:
            case 32:
                r = s[0];
                g = s[1];
                b = s[2];
                s += iDelta;
                break;
            case 16:
                r = s[1] & 0xf8; // red
                g = ((s[0] | s[1] << 8) >> 3) & 0xfc; // green
                b = s[0] << 3;
                s += 2;
                break;
                case 8:
                    if (pPalette) {
                        pPal = &pPalette[s[0] * 3];
                        r = pPal[0];
                        g = pPal[1];
                        b = pPal[2];
                    } else {
                        r = g = b = s[0];
                    }
                    s++;
                    break;
                case 4:
                    if (pPalette) {
                        if (x & 1) {
                            pPal = &pPalette[(s[0] & 0xf) * 3];
                            s++;
                        } else {
                            pPal = &pPalette[(s[0]>>4) * 3];
                        }
                        r = pPal[0];
                        g = pPal[1];
                        b = pPal[2];
                    } else {
                        if (x & 1) {
                            r = g = b = (s[0] & 0xf) | (s[0] << 4);
                            s++;
                        } else {
                            r = g = b = (s[0] >> 4) | (s[0] & 0xf0);
                        }
                    }
                    break;
                case 2:
                    if (pPalette) {
                    pPal = &pPalette[((s[0] >> ((3-(x&3))*2)) & 3) * 3];
                    r = pPal[0]; g = pPal[1]; b = pPal[2];
                    } else {
                    r = g = b = (s[0] << ((x&3)*2)) & 0xc0;
                    }
                    if ((x & 3) == 3) s++;
                    break;
                case 1:
                    if (pPalette) {
                        pPal = &pPalette[((s[0] >> (7-(x&7))) & 1) * 3];
                        r = pPal[0]; g = pPal[1]; b = pPal[2];
                    } else {
                        r = g = b = ((s[0] << (x&7)) & 0x80);
                    }
                    if ((x & 7) == 7) s++;
                    break;
            } // switch on bpp
            uc <<= 2;
            uc |= GetBWYRPixel(r, g, b); // get the best matching 2-bit color
            if ((x & 3) == 3) { // 4 pixels packed into each byte
                *d++ = uc;
            }
        } // for x
    bbep.writeData(pTemp, (pDraw->iWidth+3)/4);
    return 1; // continue decoding
} /* png_draw4clr() */
#endif // BOARD_TRMNL_4CLR (4 color only)

int png_draw(PNGDRAW *pDraw)
{
    int x;
    uint8_t ucBppChanged = 0, ucInvert = 0;
    uint8_t uc, ucMask, src, *s, *d, *pTemp = bbep.getCache(); // get some scratch memory (not from the stack)
    int iPlane = *(int *)pDraw->pUser;
    int iWidth;

    iWidth = pDraw->iWidth;
    if (pDraw->y >= bbep.height()) return 0; // stop decoding if we'll go past the bottom
    if (iWidth > bbep.width()) iWidth = bbep.width(); // crop image width to display size if it's larger

    if (pDraw->iPixelType == PNG_PIXEL_INDEXED || pDraw->iBpp > 2) {
        if (pDraw->iBpp == 1) { // 1-bit output, just see which color is brighter
            uint32_t u32Gray0, u32Gray1;
            u32Gray0 = pDraw->pPalette[0] + (pDraw->pPalette[1]<<2) + pDraw->pPalette[2];
            u32Gray1 = pDraw->pPalette[3] + (pDraw->pPalette[4]<<2) + pDraw->pPalette[5];
          if (u32Gray0 < u32Gray1) {
            ucInvert = 0xff;
          }
        } else {
            // Reduce the source image to 1-bpp or 2-bpp
            ReduceBpp((pDraw->pUser) ? 2:1, pDraw->iPixelType, pDraw->pPalette, pDraw->pPixels, pTemp, iWidth, pDraw->iBpp);
            ucBppChanged = 1;
        }
    } else if (pDraw->iBpp == 2) {
        ucInvert = 0xff; // 2-bit non-palette images need to be inverted colors for 4-gray mode
    }
    s = (ucBppChanged) ? pTemp : (uint8_t *)pDraw->pPixels;
    d = pTemp;
    if (iPlane == PNG_1_BIT || iPlane == PNG_1_BIT_INVERTED) {
        // 1-bit output, decode the single plane and write it
        if (iPlane == PNG_1_BIT_INVERTED) ucInvert = ~ucInvert; // to do PLANE_FALSE_DIFF
        if (iPlane == PNG_1_BIT_INVERTED && (bbep.capabilities() & BBEP_3COLOR)) { // write the red plane as 0's for this case
            memset(d, 0, iWidth/8);
        } else {
            for (x=0; x<iWidth; x+= 8) {
                d[0] = s[0] ^ ucInvert;
                d++; s++;
            }
        }
    } else { // we need to split the 2-bit data into plane 0 and 1
        src = *s++;
        src ^= ucInvert;
        uc = 0; // suppress warning/error
        if (iPlane == PNG_2_BIT_BOTH || iPlane == PNG_2_BIT_INVERTED) { // draw 2bpp data as 1-bit to use for partial update
            if (iPlane == PNG_2_BIT_BOTH) {
                ucInvert = ~ucInvert; // the invert rule is backwards for grayscale data
            }
            src = ~src;
            for (x=0; x<iWidth; x++) {
                uc <<= 1;
                if (src & 0xc0) { // non-white -> black
                    uc |= 1; // high bit of source pair
                }
                src <<= 2;
                if ((x & 3) == 3) { // new input byte
                    src = *s++;
                    src ^= ucInvert;
                }
                if ((x & 7) == 7) { // new output byte
                    *d++ = uc;
                }
            } // for x
        } else { // normal 0/1 split plane
            ucMask = (iPlane == PNG_2_BIT_0) ? 0x40 : 0x80; // lower or upper source bit
            for (x=0; x<iWidth; x++) {
                uc <<= 1;
                if (src & ucMask) {
                    uc |= 1; // high bit of source pair
                }
                src <<= 2;
                if ((x & 3) == 3) { // new input byte
                    src = *s++;
                    src ^= ucInvert;
                }
                if ((x & 7) == 7) { // new output byte
                    *d++ = uc;
                }
            } // for x
        }
    }
    bbep.writeData(pTemp, (iWidth+7)/8);
    return 1;
} /* png_draw() */
#else // TRMNL_X version
// The generic 2-bit gray update procedure is too dark on the X's 10.3" panel, so
// we need to use the more complex 4-bit update method which has a custom pattern
// specifically for that panel's characteristics. This loop maps 2-bit pixels to
// 4-bit pixels by converting the values 0/1/2/3 to 0/5/10/15
static void Expand2bppLineTo4bpp(const uint8_t *src, uint8_t *dest, int width)
{
    uint8_t b;
    uint16_t u16;

    for (int x = 0; x < width; x+=4) {
        u16 = 0;
        b = *src++;
        for (int j=0; j<4; j++) {
            u16 <<= 4;
            u16 |= (((b >> 6) & 3) * 5);
            b <<= 2;
        } // for j
      *dest++ = (uint8_t)(u16 >> 8);
      *dest++ = (uint8_t)(u16 & 0xff);
    } // for x
} /* Expand2bppLineTo4bpp() */

int png_draw(PNGDRAW *pDraw)
{
    int x, y = pDraw->y;
    uint8_t uc = 0;
    uint8_t ucMask, ucPixel, src, *s, *d;
    int iPitch, iBpp;

    if (y >= bbep.height() && pDraw->iWidth != bbep.height()) return 0; // image is larger than the display (and not rotated), stop decoding it
    if (pDraw->iPixelType == PNG_PIXEL_INDEXED || pDraw->iBpp > 4) { // need to convert through the palette and/or reduce the bpp
        s = bbep.tempBuffer(); // temp space we can use
        iBpp = (pDraw->iBpp > 4) ? 4 : pDraw->iBpp;
        if (iBpp == 2) iBpp = 4; // 2-bit indexed images -> 4bpp for calibrated gray refresh
        ReduceBpp(iBpp, pDraw->iPixelType, pDraw->pPalette, pDraw->pPixels, s, pDraw->iWidth, pDraw->iBpp);
    } else { // for grayscale images of 1/2/4-bpp we can directly use the pixels as-is
        iBpp = pDraw->iBpp;
        s = (uint8_t *)pDraw->pPixels;
    }
    if (pDraw->pUser) { // drawing previous image into previous buffer
        d = bbep.previousBuffer();
        switch (iBpp) { // if this matches the new image we can do a non-flickering update
            case 1:
                bbep.setPreviousMode(BB_MODE_1BPP);
                break;
            default:
                bbep.setPreviousMode(BB_MODE_4BPP);
                break;
        }
    } else {
        d = bbep.currentBuffer();
    }
    iPitch = bbep.width()/2;
    if (iBpp == 1) {
        if (bbep.width() >= pDraw->iWidth) { // normal orientation
            iPitch = (bbep.width() + 7)/8;
            d += y * iPitch; // point to the correct line
            memcpy(d, s, (pDraw->iWidth+7)/8);
        } else { // rotated
            uint8_t ucPixel, ucMask, j;
            d += (bbep.height() - 1) * iPitch;
            d += (y / 8);
            ucMask = 0x80 >> (y & 7); // destination mask
            for (x=0; x<pDraw->iWidth; x++) {
                if ((x & 7) == 0) uc = *s++;
                ucPixel = d[0] & ~ucMask; // unset old pixel
                if (uc & 0x80) ucPixel |= ucMask;
                d[0] = ucPixel;
                uc <<= 1;
                d -= iPitch;
            }
        }
    } else {
        if (iBpp == 2) { // expand 2-bit grayscale to 4-bit for calibrated refresh
            Expand2bppLineTo4bpp(s, bbep.tempBuffer(), pDraw->iWidth);
            s = bbep.tempBuffer();
            iBpp = 4;
        }
        // 4-bit native format (includes expanded 2-bit)
        if (bbep.width() == pDraw->iWidth) { // normal orientation
            d += y * iPitch; // point to the correct line
            memcpy(d, s, (pDraw->iWidth+1)/2);
        } else { // rotated
            d += (bbep.height() - 1) * iPitch;
            d += (y / 2);
            if (y & 1) { // odd line (column)
                for (x=0; x<pDraw->iWidth; x+=2) {
                    uc = (d[0] & 0xf0) | (s[0] >> 4);
                    *d = uc;
                    d -= iPitch;
                    uc = (d[0] & 0xf0) | (s[0] & 0xf);
                    *d = uc;
                    d -= iPitch;
                    s++;
                } // for x
            } else {
                for (x=0; x<pDraw->iWidth; x+=2) {
                    uc = (d[0] & 0xf) | (s[0] & 0xf0);
                    *d = uc;
                    d -= iPitch;
                    uc = (d[0] & 0xf) | (s[0] << 4);
                    *d = uc;
                    d -= iPitch;
                    s++;
                } // for x
            }
        }
    }
    return 1;
} /* png_draw() */
#endif
//
// A table to accelerate the testing of 2-bit images for the number
// of unique colors. Each entry sets bits 0-3 depending on the presence
// of colors 0-3 in each 2-bit pixel
//
const uint8_t ucTwoBitFlags[256] = {
0x01,0x03,0x05,0x09,0x03,0x03,0x07,0x0b,0x05,0x07,0x05,0x0d,0x09,0x0b,0x0d,0x09,
0x03,0x03,0x07,0x0b,0x03,0x03,0x07,0x0b,0x07,0x07,0x07,0x0f,0x0b,0x0b,0x0f,0x0b,
0x05,0x07,0x05,0x0d,0x07,0x07,0x07,0x0f,0x05,0x07,0x05,0x0d,0x0d,0x0f,0x0d,0x0d,
0x09,0x0b,0x0d,0x09,0x0b,0x0b,0x0f,0x0b,0x0d,0x0f,0x0d,0x0d,0x09,0x0b,0x0d,0x09,
0x03,0x03,0x07,0x0b,0x03,0x03,0x07,0x0b,0x07,0x07,0x07,0x0f,0x0b,0x0b,0x0f,0x0b,
0x03,0x03,0x07,0x0b,0x03,0x02,0x06,0x0a,0x07,0x06,0x06,0x0e,0x0b,0x0a,0x0e,0x0a,
0x07,0x07,0x07,0x0f,0x07,0x06,0x06,0x0e,0x07,0x06,0x06,0x0e,0x0f,0x0e,0x0e,0x0e,
0x0b,0x0b,0x0f,0x0b,0x0b,0x0a,0x0e,0x0a,0x0f,0x0e,0x0e,0x0e,0x0b,0x0a,0x0e,0x0a,
0x05,0x07,0x05,0x0d,0x07,0x07,0x07,0x0f,0x05,0x07,0x05,0x0d,0x0d,0x0f,0x0d,0x0d,
0x07,0x07,0x07,0x0f,0x07,0x06,0x06,0x0e,0x07,0x06,0x06,0x0e,0x0f,0x0e,0x0e,0x0e,
0x05,0x07,0x05,0x0d,0x07,0x06,0x06,0x0e,0x05,0x06,0x04,0x0c,0x0d,0x0e,0x0c,0x0c,
0x0d,0x0f,0x0d,0x0d,0x0f,0x0e,0x0e,0x0e,0x0d,0x0e,0x0c,0x0c,0x0d,0x0e,0x0c,0x0c,
0x09,0x0b,0x0d,0x09,0x0b,0x0b,0x0f,0x0b,0x0d,0x0f,0x0d,0x0d,0x09,0x0b,0x0d,0x09,
0x0b,0x0b,0x0f,0x0b,0x0b,0x0a,0x0e,0x0a,0x0f,0x0e,0x0e,0x0e,0x0b,0x0a,0x0e,0x0a,
0x0d,0x0f,0x0d,0x0d,0x0f,0x0e,0x0e,0x0e,0x0d,0x0e,0x0c,0x0c,0x0d,0x0e,0x0c,0x0c,
0x09,0x0b,0x0d,0x09,0x0b,0x0a,0x0e,0x0a,0x0d,0x0e,0x0c,0x0c,0x09,0x0a,0x0c,0x08
};

int png_draw_count(PNGDRAW *pDraw)
{
    int x, *pFlags = (int *)pDraw->pUser;
    uint8_t *s, set_bits;

    if (pDraw->y > 430) return 0; // Workaround to ignore the icon in the lower left corner

    set_bits = pFlags[0]; // use a local var
    s = (uint8_t *)pDraw->pPixels;
    for (x=0; x<pDraw->iWidth; x+=4) {
        set_bits |= ucTwoBitFlags[*s++]; // do 4 pixels at a time
    } // for x
    pFlags[0] = set_bits; // put it back in the flags array
    return 1;
} /* png_draw_count() */
/**
 * @brief Function to decode a PNG and count the number of unique colors
 *        This is needed because 2-bit (4gray) images can sometimes contain
 *        only 2 unique colors. This will allow us to use partial (non-flickering)
 *        updates on these images.
 * @param pointer to the PNG class instance
 * @param pointer to the buffer holding the PNG file
 * @param size of the PNG file
 * @return the number of unique colors in the image (2 to 4)
 */
int png_count_colors(PNG *png, const uint8_t *pData, int iDataSize)
{
int i, iColors;
    png->openRAM((uint8_t *)pData, iDataSize, png_draw_count);
    i = 0;
    png->decode(&i, 0);
    png->close();
    iColors = 0;
    if (i & 1) iColors++;
    if (i & 2) iColors++;
    if (i & 4) iColors++;
    if (i & 8) iColors++;
    Log_info("%s [%d]: png_count_colors: %d\r\n", __FILE__, __LINE__, iColors);
    return iColors;
} /* png_count_colors() */

/**
 * @brief JPEGDEC callback function passed blocks of MCUs (minimum coded units)
 * @param pointer to the JPEGDRAW structure
 * @return 1 to continue decoding or 0 to abort
 */
int jpeg_draw(JPEGDRAW *pDraw)
{
#ifdef BB_EPAPER
int x, y;
int iPlane = *(int *)pDraw->pUser;
uint8_t src=0, uc=0, ucMask, *s, *d, *pTemp = bbep.getCache();

    bbep.setAddrWindow(pDraw->x, pDraw->y, pDraw->iWidth, pDraw->iHeight);
    if (iPlane == 0) { // 1-bit mode
        bbep.startWrite(PLANE_0); // start writing image data to plane 0
        for (y=0; y<pDraw->iHeight; y++) { // this is 8 or 16 depending on the color subsampling
            s = (uint8_t *)pDraw->pPixels;
            s += (y * (pDraw->iWidth >> 3));
            // The pixel format of the display is the same as JPEGDEC, so just copy it
            bbep.writeData(s, (pDraw->iWidth+7)/8);
        } // for y
    } else {
        bbep.startWrite((iPlane == 1) ? PLANE_0 : PLANE_1); // start writing image data to plane 0
        for (y=0; y<pDraw->iHeight; y++) { // this is 8 or 16 depending on the color subsampling
            d = pTemp;
            s = (uint8_t *)pDither;
            s += (y * (pDraw->iWidth >> 2));
            ucMask = (iPlane == 1) ? 0x40 : 0x80; // lower or upper source bit
            for (x=0; x<pDraw->iWidth; x++) {
                if ((x & 3) == 0) { // new input byte
                    src = *s++;
                }
                uc <<= 1;
                if (src & ucMask) {
                    uc |= 1; // high bit of source pair
                }
                src <<= 2;
                if ((x & 7) == 7) { // new output byte
                    *d++ = uc;
                }
            } // for x
            bbep.writeData(pTemp, (pDraw->iWidth+7)/8);
        } // for y
    }
#else // FastEPD
  int x, y, iPitch = bbep.width()/2; // assume 4-bpp drawing mode
  uint8_t *s, *d, *pBuffer = bbep.currentBuffer();
  for (y=0; y<pDraw->iHeight; y++) {
    d = &pBuffer[((pDraw->y + y)*iPitch) + (pDraw->x/2)];
    s = (uint8_t *)pDraw->pPixels;
    s += (y * (pDraw->iWidth/2));
    memcpy(d, s, pDraw->iWidth/2); // source & dest format are the same
  } // for y
#endif
    return 1; // continue decoding
} /* jpeg_draw() */
/**
 * @brief Function to decode and display a JPEG image from memory
 *        The decoded lines are written directly into the EPD framebuffer
 *        due to insufficient RAM to hold the fully decoded image
 * @param pointer to the buffer holding the JPEG file
 * @param size of the JPEG file
 * @return refresh mode based on image type and presence of old image
 */
int jpeg_to_epd(const uint8_t *pJPEG, int iDataSize)
{
JPEGDEC *jpg = new JPEGDEC();
int rc = -1; // invalid mode
int iPlane = 0;

    if (!jpg) {
        Log_error("%s [%d]: Not enough memory for the JPEG decoder instance", __FILE__, __LINE__);
        return JPEG_ERROR_MEMORY; // not enough memory for the decoder instance
    }
    rc = jpg->openRAM((uint8_t *)pJPEG, iDataSize, jpeg_draw);
    if (rc) {
        if (jpg->getWidth() != bbep.width() || jpg->getHeight() != bbep.height()) {
            Log_error("JPEG image size doesn't match display size");
            rc = -1;
        } else { // okay to decode
#ifdef BB_EPAPER
            //bbep.setPanelType(TWO_BIT_PANEL);
            Log_info("%s [%d]: Decoding jpeg as 1-bpp dithered\r\n", __FILE__, __LINE__);
            jpg->setPixelType(ONE_BIT_DITHERED); // request 1-bit dithered output
#else
            bbep.setMode(BB_MODE_4BPP);
            Log_info("%s [%d]: Decoding jpeg as 4-bpp dithered\r\n", __FILE__, __LINE__);
            jpg->setPixelType(FOUR_BIT_DITHERED); // request 4-bit dithered output
#endif
            pDither = (uint8_t *)malloc(jpg->getWidth() * 16);
            iPlane = 0;//1; // Decode first plane
            Log_info("%s [%d]: Decoding plane 0\r\n", __FILE__, __LINE__);
            jpg->setUserPointer((void *)&iPlane);
            jpg->decodeDither(pDither, 0);
            jpg->close();
            // Decode the second plane
//            iPlane = 2;
//            Log_info("%s [%d]: Decoding plane 1\r\n", __FILE__, __LINE__);
//            jpg->openRAM((uint8_t *)pJPEG, iDataSize, jpeg_draw);
//            jpg->setPixelType(TWO_BIT_DITHERED); // request 1-bit dithered output
//            jpg->setUserPointer((void *)&iPlane);
//            jpg->decodeDither(pDither, 0);
            free(pDither);
#ifdef BB_EPAPER
            rc = REFRESH_FULL;
#endif
        }
    }
    jpg->close();
    delete(jpg);
    return rc;
} /* jpeg_to_epd() */
/**
 * @brief Function to decode and display a PNG image from memory
 *        The decoded lines are written directly into the EPD framebuffer
 *        due to insufficient RAM to hold the fully decoded image
 * @param pointer to the buffer holding the PNG file
 * @param size of the PNG file
 * @return refresh mode based on image type and presence of old image
 */
int png_to_epd(const uint8_t *pPNG, int iDataSize, bool bPrevious)
{
int iPlane = PNG_1_BIT, rc = -1;
PNG *png = new PNG();

#ifndef BB_EPAPER
    if (bPrevious && bbep.getPreviousMode() != BB_MODE_NONE) return 0; // no need to decode previous image, we drew a msg/glyph
#endif

    if (!png) return PNG_MEM_ERROR; // not enough memory for the decoder instance
    rc = png->openRAM((uint8_t *)pPNG, iDataSize, png_draw);
    png->close();
    if (rc == PNG_SUCCESS) {
        Log_info("Decoding %d x %d PNG", png->getWidth(), png->getHeight());
        if (png->getWidth() == bbep.height() && png->getHeight() == bbep.width()) {
            Log_info("Rotating canvas to portrait orientation");
        } else if (png->getWidth() > bbep.width() || png->getHeight() > bbep.height()) {
            Log_info("PNG image is larger than the display (%dx%d), it will be cropped", png->getWidth(), png->getHeight());
        }
        if (rc == PNG_SUCCESS) { // okay to decode
            Log_info("%s [%d]: Decoding %d-bpp png (current)\r\n", __FILE__, __LINE__, png->getBpp());
            // Prepare target memory window (entire display)
#ifdef BB_EPAPER
            if (bbep.capabilities() & BBEP_7COLOR) { // Spectra6 panels
                CreateSpectra6Pal(); // create a fast color matching palette
                if (bbep.allocBuffer() != BBEP_SUCCESS) {
                    Log_error("%s [%d]: bbep.AllocBuffer failed!\n\r", __FILE__, __LINE__);
                    return -1;
                }
                Log_info("%s [%d]: decoding for 6-color EPD\r\n", __FILE__, __LINE__);
                png->openRAM((uint8_t *)pPNG, iDataSize, png_draw_6clr);
                png->decode(NULL, 0);
                png->close();
                delete(png); // free the decoder instance
                bbep.writePlane(); // send the pixels to the display panel
                return REFRESH_FAST;
            }
#ifdef BOARD_TRMNL_4CLR
            Log_info("%s [%d]: decoding for 4-color EPD\r\n", __FILE__, __LINE__);
            png->openRAM((uint8_t *)pPNG, iDataSize, png_draw_4clr);
            bbep.startWrite(PLANE_1); // start writing image data
            png->decode(NULL, 0);
            png->close();
            delete(png); // free the decoder instance
            return REFRESH_FULL;
#endif // BOARD_TRMNL_4CLR
            bbep.setAddrWindow(0, 0, bbep.width(), bbep.height());
            if (png->getBpp() == 1 || (png->getBpp() == 2 && png_count_colors(png, pPNG, iDataSize) == 2)) { // 1-bit image (single plane)
                png->close(); // use a different PNGDraw callback for color matching
                bbep.setPanelType(dpList[pDevice->panel_set][iTempProfile].OneBit);
                rc = REFRESH_PARTIAL; // the new image is 1bpp - try a partial update
                bbep.startWrite(PLANE_0); // start writing image data to plane 0
                png->openRAM((uint8_t *)pPNG, iDataSize, png_draw);
                if (png->getBpp() == 1 || png->getBpp() > 2) {
                    iPlane = PNG_1_BIT;
                    png->decode(&iPlane, 0);
                } else { // convert the 2-bit image to 1-bit output
                    Log_info("%s [%d]: Current png only has 2 unique colors!\n", __FILE__, __LINE__);
                    iPlane = PNG_2_BIT_BOTH;
                    if (png->decode(&iPlane, 0) != PNG_SUCCESS) {
                        Log_info("%s [%d]: Error decoding image = %d\n", __FILE__, __LINE__, png->getLastError());
                    }
                }
                png->close();
                if (bbep.getPanelType() != EP75_800x480) { // need to write the inverted plane to do PLANE_FALSE_DIFF
                    bbep.startWrite(PLANE_1); // start writing image data to plane 1
                    png->openRAM((uint8_t *)pPNG, iDataSize, png_draw);
                    if (iPlane == PNG_1_BIT) {
                        iPlane = PNG_1_BIT_INVERTED; // inverted 1-bit to second memory plane
                    } else { // convert the 2-bit image to 1-bit output
                        iPlane = PNG_2_BIT_INVERTED; // inverted 2-bit -> 1-bit to second plane
                    }
                    png->decode(&iPlane, 0);
                } // temp profile needs the second plane written
            } else { // 2-bpp (or greater, but reduced to 2-bpp)
                if (pDevice->epd_mosi_pin != 0 || pDevice->epd_sck_pin != 0) {
                    bbep.setPanelType(dpList[pDevice->panel_set][iTempProfile].TwoBit);
                    bbep.initIO(pDevice->epd_dc_pin, pDevice->epd_rst_pin, pDevice->epd_busy_pin, pDevice->epd_cs_pin,
                    pDevice->epd_mosi_pin, pDevice->epd_sck_pin, 8000000);
                } else {
                    bbep.begin(dpList[pDevice->panel_set][0].TwoBit);
                }
                rc = REFRESH_FULL; // 4gray mode must be full refresh
                iUpdateCount = 0; // grayscale mode resets the partial update counter
                bbep.startWrite(PLANE_0); // start writing image data to plane 0
                iPlane = PNG_2_BIT_0;
                Log_info("%s [%d]: decoding 4-gray plane 0\r\n", __FILE__, __LINE__);
                png->openRAM((uint8_t *)pPNG, iDataSize, png_draw);
                png->decode(&iPlane, 0); // tell PNGDraw to use bits for plane 0
                png->close(); // start over for plane 1
                iPlane = PNG_2_BIT_1;
                Log_info("%s [%d]: decoding 4-gray plane 1\r\n", __FILE__, __LINE__);
                png->openRAM((uint8_t *)pPNG, iDataSize, png_draw);
                bbep.startWrite(PLANE_1); // start writing image data to plane 1
                png->decode(&iPlane, 0); // decode it again to get plane 1 data
            }
#else // FastEPD
            switch (png->getBpp()) {
                case 1:
                    bbep.setMode(BB_MODE_1BPP);
                break;
                case 2:
                    // 2-bit PNGs are expanded to 4bpp in png_draw() so refresh uses u8_graytable
                    bbep.setMode(BB_MODE_4BPP);
                break;
                default:
                    bbep.setMode(BB_MODE_4BPP);
                break;
            }
            Log_info("%s [%d]: FastEPD graphics mode set to: %d\n", __FILE__, __LINE__, bbep.getMode());
            png->decode((void *)bPrevious, 0);
            png->close();
#endif
        }
    } else {
        Log_error("%s [%d]: png->openRAM() returned %d", __FILE__, __LINE__, rc);
    }
    delete(png); // free the decoder instance
    return rc;
} /* png_to_epd() */
/**
 * @brief Function to show the image on the display
 * @param image_buffer pointer to the uint8_t image buffer
 * @param reverse shows if the color scheme is reverse
 * @return none
 */
void display_show_image(uint8_t *image_buffer, int data_size, bool bWait, bool bSkipClear)

{
    bool isPNG = data_size >= 4 && MOTOLONG(image_buffer) == (int32_t)0x89504e47;
    auto width = display_width();
    auto height = display_height();
//    uint32_t *d32;
    bool bAlloc = false;
    static int i426Workaround = 0;
#ifdef BB_EPAPER
    int iRefreshMode = REFRESH_FULL; // assume full (slow) refresh
#else
    int iRefreshMode = 0;
#endif

   // Log_info("Paint_NewImage %d", reverse);
    Log_info("display_show_image start");
    Log_info("maximum_compatibility = %d\n", apiDisplayResult.response.maximum_compatibility);
#ifdef FUTURE
    if (reverse)
    {
        d32 = (uint32_t *)image_buffer; // get framebuffer as a 32-bit pointer
        d32 = (uint32_t *)image_buffer; // get framebuffer as a 32-bit pointer
        Log_info("inverse the image");
        for (size_t i = 0; i < buf_size; i+=sizeof(uint32_t))
        for (size_t i = 0; i < buf_size; i+=sizeof(uint32_t))
        {
            d32[0] = ~d32[0];
            d32++;
            d32[0] = ~d32[0];
            d32++;
        }
    }
#endif
#ifdef BB_EPAPER
    if (pDevice->epd_mosi_pin != 0 || pDevice->epd_sck_pin != 0) {
        bbep.setPanelType(dpList[pDevice->panel_set][iTempProfile].OneBit);
        bbep.initIO(pDevice->epd_dc_pin, pDevice->epd_rst_pin, pDevice->epd_busy_pin, pDevice->epd_cs_pin,
            pDevice->epd_mosi_pin, pDevice->epd_sck_pin, 8000000);
    } else {
        bbep.begin(dpList[pDevice->panel_set][0].OneBit);
    }
#endif // BB_EPAPER
    if (isPNG == true && data_size < MAX_IMAGE_SIZE)
    {
        Log_info("Drawing PNG");
        iRefreshMode = png_to_epd(image_buffer, data_size, false);
    }
    else if (MOTOSHORT(image_buffer) == 0xffd8) {
        Log_info("Drawing JPEG");
        iRefreshMode = jpeg_to_epd(image_buffer, data_size);
    }
    else // uncompressed BMP or Group5 compressed image
    {
        if (*(uint16_t *)image_buffer == BB_BITMAP_MARKER)
        {
            // G5 compressed image
            BB_BITMAP *pBBB = (BB_BITMAP *)image_buffer;
#ifdef BB_EPAPER
            if (bbep.allocBuffer(false) != BBEP_SUCCESS) {
                Log_info("Error allocating bb_epaper frame buffer");
                return;
            }
            bAlloc = true;
#endif
        //    int x = (width - pBBB->width)/2;
        //    int y = (height - pBBB->height)/2; // center it
        // place it in the lower right corner
            int x = (width - pBBB->width);
            int y = (height - pBBB->height);
            if (x > 0 || y > 0) // only clear if the image is smaller than the display
            {
                bbep.fillScreen(BBEP_WHITE);
            }
            bbep.loadG5Image(image_buffer, x, y, BBEP_WHITE, BBEP_BLACK);
#ifdef BOARD_TRMNL_X
            // Show charging indicator if the USB power is connected (whether actually charging or not)
            if (power().usbStatus() == UsbStatus::CONNECTED) {
                Log_info("Displaying 'battery is charging' icon");
                bbep.loadG5Image(battery_small, 40, bbep.height() - 120, BBEP_WHITE, BBEP_BLACK);
            } else { // show battery level
                y = bbep.height() - 120;
                bbep.loadG5Image(battery_hollow, 40, y, BBEP_WHITE, BBEP_BLACK);
                Log_info("Displaying 'battery charge level' icon");
                int batt_percent = battery().readSoc(); // -1 if no battery or the gauge reading failed
                if (batt_percent >= 0) {
                    if (batt_percent >= 97) batt_percent = 100; // can sometimes report 98% when full
                    // Draw a black rectangle to represent the battery charge level
                    bbep.fillRect(40+10, y+18, (97 * batt_percent)/100, 39, BBEP_BLACK);
                } else {
                    bbep.drawLine(40+10, y+18, 10+97, y+18+39, BBEP_BLACK);
                    bbep.drawLine(40+10+97, y+18, 10, y+18+39, BBEP_BLACK);
                }
            }
#endif // BOARD_TRMNL_X
        }
        else
        {
         // This work-around is due to a lack of RAM; the correct method would be to use loadBMP()
            flip_image(image_buffer+62, bbep.width(), bbep.height(), false); // fix bottom-up bitmap images
#ifdef BB_EPAPER
            bbep.setBuffer(image_buffer+62); // uncompressed 1-bpp bitmap
#endif // BB_EPAPER
        }
#ifdef BB_EPAPER
#ifndef BOARD_SEEED_RETERMINAL_E1002
        bbep.writePlane(); // send image data to the EPD
#endif // !BOARD_SEEED_RETERMINAL_E1002
        iRefreshMode = REFRESH_PARTIAL;
#endif // BB_EPAPER
        iUpdateCount = 1; // use partial update
    }
    Log_info("Display refresh start");
    if (iTempProfile != apiDisplayResult.response.temp_profile) {
        iTempProfile = apiDisplayResult.response.temp_profile;
        Log_info("Saving new temperature profile (%" PRIu32 ") to FLASH", iTempProfile);
        preferences.putUInt(PREFERENCES_TEMP_PROFILE, iTempProfile);
    }
#ifdef BB_EPAPER
    if ((iUpdateCount & 7) == 0 || apiDisplayResult.response.maximum_compatibility == true) {
        Log_info("%s [%d]: Forcing full refresh; desired refresh mode was: %d\r\n", __FILE__, __LINE__, iRefreshMode);
        iRefreshMode = REFRESH_FULL; // force full refresh every 8 partials
    }
    int refresh_seconds = refreshInterval.seconds();
    if (refresh_seconds >= 30*60 && iRefreshMode == REFRESH_PARTIAL) {
        // For users who set updates 30 minutes or longer, use the "fast" update to prevent ghosting
        Log_info("%s [%d]: Forcing fast refresh (not partial) since the TRMNL refresh_rate is set to > 30 min\n", __FILE__, __LINE__);
        iRefreshMode = REFRESH_FAST;
    }
    if (bbep.capabilities() & (BBEP_4GRAY | BBEP_4COLOR | BBEP_3COLOR | BBEP_7COLOR)) bWait = 1;
    if (!bWait) {
        iRefreshMode = REFRESH_FAST; // fast update when showing loading screen
    }
    Log_info("%s [%d]: EPD refresh mode: %d\r\n", __FILE__, __LINE__, iRefreshMode);
#ifndef BOARD_SEEED_RETERMINAL_E1002
#ifdef DO_NOT_LIGHT_SLEEP
    bbep.setLightSleep(false);
#else
    bbep.setLightSleep(true);

#endif // DO_NOT_LIGHT_SLEEP
#endif // !BOARD_SEEED_RETERMINAL_E1002
    if (bbep.getPanelType() == EP397_800x480 && iRefreshMode == REFRESH_FAST) {
        // Seeed Sticky: fast refresh on this panel isn't working and full refresh = fast
        iRefreshMode = REFRESH_FULL;
    }
    if (!display_update_epaper(iRefreshMode, bWait)) {
        Log_error("display_show_image: e-paper update failed");
        if (bAlloc) {
            bbep.freeBuffer();
        }
        return;
    }

    if ((bbep.getPanelType() == EP426_800x480 || bbep.getPanelType() == EP426_800x480_4GRAY || bbep.getPanelType() == EP397_800x480 || bbep.getPanelType() == EP397_800x480_4GRAY) /* && iRefreshMode == REFRESH_PARTIAL*/) {
        i426Workaround = 1; // need to re-initialize the controller for another update before sleeping
    }
    if (bAlloc) {
        bbep.freeBuffer();
    }
#else
 {
    int rc = bbep.setCustomMatrix(u8_graytable, sizeof(u8_graytable));
    Log_info("%s [%d]: setCustomMatrix returned %d\r\n", __FILE__, __LINE__, rc);

 //   if (bbep.getPreviousMode() != BB_MODE_NONE && (bbep.getMode() == BB_MODE_1BPP || bbep.getMode() == BB_MODE_2BPP)) {
 //       Log_info("%s [%d]: Using partial update since we have a copy of the previous image\n", __FILE__, __LINE__);
 //       bbep.setPasses(6,6);
 //       bbep.partialUpdate(false); // we have a previous image to diff against; use a non-flickering update
 //   } else {
        // bWait=false means loading screen: skip clearing passes so it appears
        // faster. Ghosting from the previous image is acceptable since the
        // real content refresh (bWait=true) immediately follows.
        int iClearMode = bSkipClear ? CLEAR_NONE
                                   : ((iUpdateCount & 7) == 0 || (iTempProfile > 0)) ? CLEAR_SLOW : CLEAR_FAST;
        Log_info("fullUpdate clear mode = %d\n", iClearMode);
        bbep.fullUpdate(iClearMode, false);
 //   }
 }
#endif
    iUpdateCount++;
    Log_info("display_show_image end");
}
/**
 * @brief Function to read an image from the file system
 * @param filename
 * @param pointer to file size returned
 * @return pointer to allocated buffer
 */
uint8_t * display_read_file(const char *filename, int *file_size)
{
File f = FS.open(filename, "r");
uint8_t *buffer;

  if (!f) {
    Serial.println("Failed to open file!");
    *file_size = 0;
    return nullptr;
  }
  *file_size = f.size();
  if (*file_size == 0) {
    Serial.println("File is empty!");
    f.close();
    return nullptr;
  }
  Serial.printf("File size to allocate: %d bytes\n", *file_size);
  #ifdef CONFIG_SPIRAM
  Serial.println("Allocating file buffer in PSRAM");
  buffer = (uint8_t *)ps_malloc(*file_size);
  #else
  Serial.println("Allocating file buffer in regular RAM");
  buffer = (uint8_t *)malloc(*file_size);
  #endif
  if (!buffer) {
    Serial.println("Memory allocation failed!");
    *file_size = 0;
    return nullptr;
  }
  f.read(buffer, *file_size);
  f.close();
  return buffer;
} /* display_read_file() */

/**
 * @brief Function to show the image with message on the display
 * @param image_buffer pointer to the uint8_t image buffer
 * @param message_type type of message that will show on the screen
 * @return none
 */
void display_show_msg(uint8_t *image_buffer, MSG message_type, const char *message_text)
{
    auto width = display_width();
    auto height = display_height();
    UWORD Imagesize = ((width % 8 == 0) ? (width / 8) : (width / 8 + 1)) * height;
    BB_RECT rect;

    Log_info("display_show_msg start");
    Log_info("maximum_compatibility = %d\n", apiDisplayResult.response.maximum_compatibility);
#ifdef BB_EPAPER
    bbep.allocBuffer(false);
#else
    bbep.setMode(BB_MODE_1BPP); // message screens are 1-bit
#endif
    if (image_buffer && *(uint16_t *)image_buffer == BB_BITMAP_MARKER)
    {
        // G5 compressed image
        BB_BITMAP *pBBB = (BB_BITMAP *)image_buffer;
        int x = (width - pBBB->width)/2;
        int y = (height - pBBB->height)/2; // center it
        if (x > 0 || y > 0) // only clear if the image is smaller than the display
        {
            bbep.fillScreen(BBEP_WHITE);
        }
        bbep.loadG5Image(image_buffer, x, y, BBEP_WHITE, BBEP_BLACK);
    }
    else
    {
#ifdef BB_EPAPER
        if (image_buffer) memcpy(bbep.getBuffer(), image_buffer+62, Imagesize); // uncompressed 1-bpp bitmap
#endif
    }

#ifdef PARALLEL_EPD
    bbep.setFont(Inter_18);
#else
    bbep.setFont(nicoclean_8);
#endif
    bbep.setTextColor(BBEP_BLACK, BBEP_WHITE);

    switch (message_type)
    {
    case OTG_TURNED_ON:
    {
        const char string1[] = "OTG turned on!";
        bbep.getStringBox(string1, &rect);
        bbep.setCursor((bbep.width() - rect.w)/2, 430);
        bbep.println(string1);
    break;
    }
    case OTG_TURNED_OFF:
    {
        const char string1[] = "OTG turned off!";
        bbep.getStringBox(string1, &rect);
        bbep.setCursor((bbep.width() - rect.w)/2, 430);
        bbep.println(string1);
    break;
    }
    case MODEM_FLASHING:
    {
        const char string1[] = "Flashing modem firmware...";
        bbep.getStringBox(string1, &rect);
        bbep.setCursor((bbep.width() - rect.w)/2, 430);
        bbep.println(string1);
    break;
    }
    case MODEM_FLASH_FAILED:
    {
        const char string1[] = "Failed to flash modem firmware,";
        bbep.getStringBox(string1, &rect);
        bbep.setCursor((bbep.width() - rect.w)/2, 430);
        bbep.println(string1);

        const char string2[] = "device would only operate with 2.4Ghz WiFi.";
        bbep.getStringBox(string2, &rect);
        bbep.setCursor((bbep.width() - rect.w)/2, 500);
        if (message_text) {
            bbep.println(string2);
            bbep.getStringBox(message_text, &rect);
            bbep.setCursor((bbep.width() - rect.w)/2, 570);
            bbep.print(message_text);
        } else {
            bbep.print(string2);
        }
    break;
    }
    case READY_TO_SHIP:
    {
        const char string1[] = "Device is ready to ship!";
        bbep.getStringBox(string1, &rect);
        bbep.setCursor((bbep.width() - rect.w)/2, 430);
        bbep.println(string1);

        const char string2[] = "Unplug the USB-C to enter shipping mode.";
        bbep.getStringBox(string2, &rect);
        bbep.setCursor((bbep.width() - rect.w)/2, 500);
        bbep.print(string2);
    break;
    }
    case SHIPPING_MODE:
    {
        const char string1[] = "Welcome to TRMNL.";
        bbep.getStringBox(string1, &rect);
        bbep.setCursor((bbep.width() - rect.w)/2, 430);
        bbep.println(string1);

        const char string2[] = "Attach the dock and a USB-C to get started.";
        bbep.getStringBox(string2, &rect);
        bbep.setCursor((bbep.width() - rect.w)/2, 500);
        bbep.print(string2);
    break;
    }
    case WIFI_RESET_CONFIRM:
    {
        const char string1[] = "Are you sure you want to reset WiFi settings?";
        bbep.getStringBox(string1, &rect);
        bbep.setCursor((bbep.width() - rect.w)/2, 430);
        bbep.println(string1);
        const char string2[] = "Hold middle of touch bar to confirm, tap to cancel.";
        bbep.getStringBox(string2, &rect);
        bbep.setCursor((bbep.width() - rect.w)/2, -1);
        bbep.print(string2);
    break;
    }

    case POWER_OFF_CONFIRM:
    {
        const char string1[] = "Turn off device?";
        bbep.getStringBox(string1, &rect);
        bbep.setCursor((bbep.width() - rect.w)/2, 430);
        bbep.println(string1);
        const char string2[] = "Hold middle of touch bar to confirm, tap to cancel.";
        bbep.getStringBox(string2, &rect);
        bbep.setCursor((bbep.width() - rect.w)/2, -1);
        bbep.print(string2);
    break;
    }

    case WIFI_CONNECT:
    {
        const char string1[] = "Connect to TRMNL WiFi";
        bbep.getStringBox(string1, &rect);
        bbep.setCursor((bbep.width() - rect.w)/2, 430);
        bbep.println(string1);
        const char string2[] = "on your phone or computer";
        bbep.getStringBox(string2, &rect);
        bbep.setCursor((bbep.width() - rect.w)/2, -1);
        bbep.print(string2);
    }
    break;
    case WIFI_FAILED:
    {
        String string0 = "TRMNL firmware ";
        string0 += Messages::firmware_version();
#ifdef __BB_EPAPER__
        bbep.setCursor(40, 48); // place in upper left corner
#else
        bbep.setCursor(80, 104); // place in upper left corner
#endif
        bbep.println(string0);
        const char string1[] = "Can't establish WiFi connection. Will keep trying.";
        bbep.getStringBox(string1, &rect);
        bbep.setCursor((bbep.width() - rect.w)/2, bbep.height() - (rect.h*2)-140);
        bbep.println(string1);
#ifndef BOARD_TRMNL_X
        const char string2[] = "Hold button on the back to reset WiFi, or scan QR Code for help.";
#else
        const char string2[] = "Hold left and right corner of touch bar to reset WiFi, or scan QR Code for help.";
#endif
        bbep.getStringBox(string2, &rect);
        bbep.setCursor((bbep.width() - rect.w) / 2, -1);
        bbep.println(string2);
#ifdef __BB_EPAPER__
        bbep.loadG5Image(wifi_failed_qr, bbep.width() - 66 - 40, 40, BBEP_WHITE, BBEP_BLACK);
#else // bigger for X
        bbep.loadG5Image(wifi_failed_qr, bbep.width() - (66*2) - 80, 80, BBEP_WHITE, BBEP_BLACK, 2.0f);
#endif
    }
    break;
    case WIFI_INTERNAL_ERROR:
    {
        const char string1[] = "WiFi connected, but";
#ifdef __BB_EPAPER__
        int x = 132;
#else
        int x = 0;
#endif
        bbep.getStringBox(string1, &rect);
#ifdef __BB_EPAPER__
        bbep.setCursor((bbep.width() - 132 - rect.w) / 2, 340);
#else
        bbep.setCursor((bbep.width() - rect.w)/2, bbep.height() - (rect.h*2)-140);
#endif
        bbep.println(string1);
        const char string2[] = "API connection cannot be";
        bbep.getStringBox(string2, &rect);
        bbep.setCursor((bbep.width() - x - rect.w) / 2, -1);
        bbep.println(string2);
        const char string3[] = "established. Try to refresh,";
        bbep.getStringBox(string3, &rect);
        bbep.setCursor((bbep.width() - x - rect.w) / 2, -1);
        bbep.println(string3);
        const char string4[] = "or scan QR Code for help.";
        bbep.getStringBox(string4, &rect);
        bbep.setCursor((bbep.width() - x - rect.w) / 2, -1);
        bbep.print(string4);
#ifdef __BB_EPAPER__
        bbep.loadG5Image(wifi_failed_qr, 639, 336, BBEP_WHITE, BBEP_BLACK);
#else // bigger for X
        bbep.loadG5Image(wifi_failed_qr, bbep.width() - (66*2) - 80, 80, BBEP_WHITE, BBEP_BLACK, 2.0f);
#endif
    }
    break;
    case WIFI_WEAK:
    {
        const char string1[] = "WiFi connected but signal is weak";
        bbep.getStringBox(string1, &rect);
#ifdef __BB_EPAPER__
        bbep.setCursor((bbep.width() - rect.w) / 2, 400);
#else
        bbep.setCursor((bbep.width() - rect.w) / 2, bbep.height() - 140 - rect.h);
#endif
        bbep.print(string1);
    }
    break;
    case IMAGE_DOWNLOAD_FAILED:
    {
        const char string1[] = "API responded, but image download failed.";
        bbep.getStringBox(string1, &rect);
        bbep.setCursor((bbep.width() - rect.w) / 2, 340);
        bbep.println(string1);
#ifndef BOARD_TRMNL_X
        const char string2[] = "Short click the button on back";
#else
        const char string2[] = "Tap the middle of touch bar";
#endif
        bbep.getStringBox(string2, &rect);
        bbep.setCursor((bbep.width() - rect.w) / 2, -1);
        bbep.println(string2);
        const char string3[] = "to advance to the next screen.";
        bbep.getStringBox(string3, &rect);
        bbep.setCursor((bbep.width() - rect.w) / 2, -1);
        bbep.print(string3);
    }
    break;
    case API_UNABLE_TO_CONNECT:
    {
        const char string1[] = "WiFi connected, unable connect to API.";
        bbep.getStringBox(string1, &rect);
        bbep.setCursor((bbep.width() - rect.w) / 2, 340);
        bbep.println(string1);
#ifndef BOARD_TRMNL_X
        const char string2[] = "Short click the button on back,";
#else
        const char string2[] = "Tap the middle of touch bar,";
#endif
        bbep.getStringBox(string2, &rect);
        bbep.setCursor((bbep.width() - rect.w) / 2, -1);
        bbep.println(string2);
        const char string3[] = "otherwise check your internet.";
        bbep.getStringBox(string3, &rect);
        bbep.setCursor((bbep.width() - rect.w) / 2, -1);
        bbep.print(string3);
    }
    break;
    case API_SETUP_FAILED:
    {
        const char string1[] = "WiFi connected, /api/setup returned error.";
        bbep.getStringBox(string1, &rect);
#ifdef __BB_EPAPER__
        bbep.setCursor((bbep.width() - rect.w) / 2, 340);
#else
        bbep.setCursor((bbep.width() - rect.w) / 2, bbep.height() - 140 - (rect.h*3));
#endif
        bbep.println(string1);
#ifndef BOARD_TRMNL_X
        const char string2[] = "Short click the button on back,";
#else
        const char string2[] = "Tap the middle of touch bar,";
#endif
        bbep.getStringBox(string2, &rect);
        bbep.setCursor((bbep.width() - rect.w) / 2, -1);
        bbep.println(string2);
        const char string3[] = "otherwise check your internet.";
        bbep.getStringBox(string3, &rect);
        bbep.setCursor((bbep.width() - rect.w) / 2, -1);
        bbep.print(string3);
    }
    break;
    case API_SIZE_ERROR:
    {
        const char string1[] = "WiFi connected, TRMNL content malformed.";
        bbep.getStringBox(string1, &rect);
#ifdef __BB_EPAPER__
        bbep.setCursor((bbep.width() - rect.w) / 2, 400);
#else
        bbep.setCursor((bbep.width() - rect.w) / 2, bbep.height() - 140 - (rect.h*2));
#endif
        bbep.println(string1);
#ifndef BOARD_TRMNL_X
        const char string2[] = "Wait or reset by holding button on back.";
#else
        const char string2[] = "Wait or reset by holding left and right corner of touch bar.";
#endif
        bbep.getStringBox(string2, &rect);
        bbep.setCursor((bbep.width() - rect.w) / 2, -1);
        bbep.print(string2);
    }
    break;
    case API_FIRMWARE_UPDATE_ERROR:
    {
        const char string1[] = "WiFi connected, could not get firmware update from api.";
        bbep.getStringBox(string1, &rect);
        bbep.setCursor((bbep.width() - rect.w) / 2, 400);
        bbep.println(string1);
#ifndef BOARD_TRMNL_X
        const char string2[] = "Wait or reset by holding button on back.";
#else
        const char string2[] = "Wait or reset by holding left and right corner of touch bar.";
#endif
        bbep.getStringBox(string2, &rect);
        bbep.setCursor((bbep.width() - rect.w) / 2, -1);
        bbep.print(string2);
    }
    break;
    case WIFI_IMAGE_TIMEOUT:
    {
        const char string1[] = "Image download timed out; check your network status.";
        bbep.getStringBox(string1, &rect);
#ifdef __BB_EPAPER__
        bbep.setCursor((bbep.width() - rect.w) / 2, 400);
#else
        bbep.setCursor((bbep.width() - rect.w) / 2, bbep.height() - 140 - rect.h);
#endif
        bbep.print(string1);
    }
    break;
    case API_IMAGE_DOWNLOAD_ERROR:
    {
        const char string1[] = "WiFi connected, API could not deliver image to device.";
        bbep.getStringBox(string1, &rect);
        bbep.setCursor((bbep.width() - rect.w) / 2, 400);
        bbep.println(string1);
#ifndef BOARD_TRMNL_X
        const char string2[] = "Wait or reset by holding button on back.";
#else
        const char string2[] = "Wait or reset by holding left and right corner of touch bar.";
#endif
        bbep.getStringBox(string2, &rect);
        bbep.setCursor((bbep.width() - rect.w) / 2, -1);
        bbep.print(string2);
    }
    break;
    case FW_UPDATE:
    {
        const char string1[] = "Firmware update available! Starting now...";
        bbep.getStringBox(string1, &rect);
#ifdef __BB_EPAPER__
        bbep.setCursor((bbep.width() - rect.w) / 2, 400);
#else
        bbep.setCursor((bbep.width() - rect.w) / 2, bbep.height() - 140 - rect.h);
#endif
        bbep.print(string1);
    }
    break;
    case FW_UPDATE_FAILED:
    {
        const char string1[] = "Firmware update failed. Device will restart...";
        bbep.getStringBox(string1, &rect);
#ifdef __BB_EPAPER__
        bbep.setCursor((bbep.width() - rect.w) / 2, 400);
#else
        bbep.setCursor((bbep.width() - rect.w) / 2, bbep.height() - 140 - rect.h);
#endif
        bbep.print(string1);
    }
    break;
    case FW_UPDATE_SUCCESS:
    {
        const char string1[] = "Firmware update success. Device will restart...";
        bbep.getStringBox(string1, &rect);
#ifdef __BB_EPAPER__
        bbep.setCursor((bbep.width() - rect.w) / 2, 400);
#else
        bbep.setCursor((bbep.width() - rect.w) / 2, bbep.height() - 140 - rect.h);
#endif
        bbep.print(string1);
    }
    break;
    case QA_START:
    {
        const char string1[] = "Starting QA test";
        bbep.getStringBox(string1, &rect);
        bbep.setCursor((bbep.width() - rect.w) / 2, 400);
        bbep.print(string1);
    }
    break;
    case MSG_TOO_BIG:
    {
        const char string1[] = "The image file from this URL is too large.";
        bbep.getStringBox(string1, &rect);
#ifdef __BB_EPAPER__
        bbep.setCursor((bbep.width() - rect.w) / 2, 360);
#else
        bbep.setCursor((bbep.width() - rect.w) / 2, bbep.height() - 140 - rect.h*4);
#endif
        bbep.println(string1);
        if (strlen(filename) > 40) {
            filename[40] = 0; // truncate and add elipses
            strcat(filename, "...");
        }
        bbep.getStringBox(filename, &rect);
        bbep.setCursor((bbep.width() - rect.w) / 2, -1);
        bbep.println(filename);

        const char string2[] = "PNG images can be a maximum of";
        bbep.getStringBox(string2, &rect);
        bbep.setCursor((bbep.width() - rect.w) / 2, -1);
        bbep.println(string2);
#ifdef __BB_EPAPER__
        String string3 = String(MAX_IMAGE_SIZE) + String(" bytes each and 1 or 2-bpp");
#else
        String string3 = String(MAX_IMAGE_SIZE) + String(" bytes each");
#endif
        bbep.getStringBox(string3.c_str(), &rect);
        bbep.setCursor((bbep.width() - rect.w) / 2, -1);
        bbep.print(string3);
    }
    break;
    case MSG_FORMAT_ERROR:
    {
        const char string1[] = "The image format is incorrect";
        bbep.getStringBox(string1, &rect);
#ifdef __BB_EPAPER__
        bbep.setCursor((bbep.width() - rect.w) / 2, 400);
#else
        bbep.setCursor((bbep.width() - rect.w) / 2, bbep.height() - 140 - rect.h);
#endif
        bbep.print(string1);
    }
    break;
    case TEST:
    {
        bbep.setCursor(0, 40);
        bbep.println("ABCDEFGHIYABCDEFGHIYABCDEFGHIYABCDEFGHIYABCDEFGHIY");
        bbep.println("abcdefghiyabcdefghiyabcdefghiyabcdefghiyabcdefghiy");
        bbep.println("A B C D E F G H I Y A B C D E F G H I Y A B C D E");
        bbep.println("a b c d e f g h i y a b c d e f g h i y a b c d e");
    }
    break;
    case FILL_WHITE:
    {
        Log_info("Display set to white");
#ifdef PARALLEL_EPD
        if (bbep.getMode() == BB_MODE_4BPP) {
            bbep.fillScreen(15); // in 4-bit mode, color 15 = white
        } else {
            bbep.fillScreen(BBEP_WHITE);
        }
#else
        bbep.fillScreen(BBEP_WHITE);
#endif
    }
    break;
    case WIFI_RETRY_LIMIT:
    {
        const char string1[] = "Maximum WiFi retries reached.";
        bbep.getStringBox(string1, &rect);
#ifdef __BB_EPAPER__
        bbep.setCursor((bbep.width() - rect.w) / 2, 340);
#else
        bbep.setCursor((bbep.width() - rect.w) / 2, bbep.height() - 140 - (rect.h*3));
#endif
        bbep.println(string1);
        const char string2[] = "Press button to manually refresh.";
        bbep.getStringBox(string2, &rect);
        bbep.setCursor((bbep.width() - rect.w) / 2, -1);
        bbep.println(string2);
        const char string3[] = "Hold button to reset WiFi and try another network.";
        bbep.getStringBox(string3, &rect);
        bbep.setCursor((bbep.width() - rect.w) / 2, -1);
        bbep.print(string3);
    }
        break;
    case CAPTIVE_WIFI_TIMEOUT:
    {
        const char string1[] = "Wifi Captive Portal timed out";
        bbep.getStringBox(string1, &rect);
#ifdef __BB_EPAPER__
        bbep.setCursor((bbep.width() - rect.w) / 2, 340);
#else
        bbep.setCursor((bbep.width() - rect.w) / 2, bbep.height() - 140 - (rect.h*2));
#endif
        bbep.println(string1);
#ifdef BOARD_TRMNL_X
        const char string2[] = "Tap touchbar to try again";
#else
        const char string2[] = "Press button to try again";
#endif
        bbep.getStringBox(string2, &rect);
        bbep.setCursor((bbep.width() - rect.w) / 2, -1);
        bbep.println(string2);
    }
        break;
    default:
        break;
    }
#ifdef BB_EPAPER
    if (!display_update_epaper(REFRESH_FULL, true, true, PLANE_0)) {
        Log_error("display_show_msg: e-paper update failed");
        bbep.freeBuffer();
        return;
    }
    bbep.freeBuffer();
#else
    Serial.println("FastEPD full update");
    bbep.fullUpdate(CLEAR_SLOW, true);
#endif
    Log_info("display_show_msg end");
}


void display_show_msg_qa(uint8_t *image_buffer, const float *voltage, const float *temperature, bool qa_result)
{
    auto width = display_width();
    auto height = display_height();
    UWORD Imagesize = ((width % 8 == 0) ? (width / 8) : (width / 8 + 1)) * height;
    BB_RECT rect;

    Log_info("display_show_msg start");
    Log_info("maximum_compatibility = %d\n", apiDisplayResult.response.maximum_compatibility);
#ifdef BB_EPAPER
    bbep.allocBuffer(false);
#else
    bbep.setMode(BB_MODE_1BPP);
    bbep.setTextColor(BBEP_BLACK, BBEP_WHITE);
#endif
    if (*(uint16_t *)image_buffer == BB_BITMAP_MARKER)
    {
        // G5 compressed image
        BB_BITMAP *pBBB = (BB_BITMAP *)image_buffer;
        int x = (width - pBBB->width)/2;
        int y = (height - pBBB->height)/2; // center it
        if (x > 0 || y > 0) // only clear if the image is smaller than the display
        {
            bbep.fillScreen(BBEP_WHITE);
        }
        bbep.loadG5Image(image_buffer, x, y, BBEP_WHITE, BBEP_BLACK);
    }
    else
    {
#ifdef BB_EPAPER
        memcpy(bbep.getBuffer(), image_buffer+62, Imagesize); // uncompressed 1-bpp bitmap
#endif
    }

    bbep.setFont(nicoclean_8); //Roboto_20);
    bbep.setTextColor(BBEP_BLACK, BBEP_WHITE);

    String voltageString = String("Initial voltage: ")
    + String(voltage[0], 4)
    + String(" V, ")
    + String("  Final voltage: ")
    + String(voltage[1], 4)
    + String(" V, ")
    + String("  Diff: ")
    + String(voltage[2], 4)
    + String(" V");

    String temperatureString = String("Initial temperature: ")
    + String(temperature[0], 4)
    + String(" C, ")
    + String("  Final temperature: ")
    + String(temperature[1], 4)
    + String(" C")
    + String("  Diff: ")
    + String(temperature[2], 4)
    + String(" C");


    bbep.getStringBox(voltageString.c_str(), &rect);
    bbep.setCursor((bbep.width() - rect.w) / 2, 340);
    bbep.print(voltageString);

    bbep.getStringBox(temperatureString.c_str(), &rect);
    bbep.setCursor((bbep.width() - rect.w) / 2, 370);
    bbep.print(temperatureString);

    String qaResultInstruction = (qa_result)
    ? "QA passed, press button to clear screen"
    : "QA failed, please use another board and put in failure pile for investigation";

    bbep.getStringBox(qaResultInstruction.c_str(), &rect);
    bbep.setCursor((bbep.width() - rect.w) / 2, 400);
    bbep.println(qaResultInstruction);

    String qaResultString = (qa_result) ? "PASS" : "FAIL";
    bbep.setFont(Roboto_Black_24);
    bbep.getStringBox(qaResultString.c_str(), &rect);
    bbep.setCursor((bbep.width() - rect.w) / 2, 250);
    bbep.print(qaResultString);

    #ifdef BB_EPAPER
        if (!display_update_epaper(REFRESH_FULL, true, true, PLANE_0)) {
            Log_error("display_show_msg_qa: e-paper update failed");
            bbep.freeBuffer();
            return;
        }
        bbep.freeBuffer();
    #else
        bbep.fullUpdate();
    #endif
        Log_info("display_show_msg end");
    /*
     const char string2[] = "PNG images can be a maximum of";
        bbep.getStringBox(string2, &rect);
        bbep.setCursor((bbep.width() - rect.w) / 2, -1);
        bbep.println(string2);
        String string3 = String(MAX_IMAGE_SIZE) + String(" bytes each and 1 or 2-bpp");
        bbep.getStringBox(string3.c_str(), &rect);
        bbep.setCursor((bbep.width() - rect.w) / 2, -1);
        bbep.print(string3);
    */
}

/**
 * @brief Function to show the image with message on the display
 * @param image_buffer pointer to the uint8_t image buffer
 * @param message_type type of message that will show on the screen
 * @param friendly_id device friendly ID
 * @param id shows if ID exists
 * @param fw_version version of the firmware
 * @param message additional message
 * @return none
 */
void display_show_msg(uint8_t *image_buffer, MSG message_type, String friendly_id, bool id, const char *fw_version, String message)
{
    Log_info("Free heap in display_show_msg - %" PRIu32, ESP.getMaxAllocHeap());
    Log_info("maximum_compatibility = %d\n", apiDisplayResult.response.maximum_compatibility);
#ifdef BB_EPAPER
    bbep.allocBuffer(false);
    Log_info("Free heap after bbep.allocBuffer() - %" PRIu32, ESP.getMaxAllocHeap());
#else
    bbep.setMode(BB_MODE_1BPP); // message screens are 1-bit
#endif

    if (message_type == WIFI_CONNECT)
    {
        Log_info("Display set to white");
        bbep.fillScreen(BBEP_WHITE);
#ifdef BB_EPAPER
        if (!display_update_epaper(apiDisplayResult.response.maximum_compatibility ? REFRESH_FULL : REFRESH_FAST, true, true, PLANE_0)) {
            Log_error("display_show_msg: WiFi connect update failed");
            bbep.freeBuffer();
            return;
        }
#else
        bbep.fullUpdate();
#endif
        display_sleep(1000);
    }

    auto width = display_width();
    auto height = display_height();
    UWORD Imagesize = ((width % 8 == 0) ? (width / 8) : (width / 8 + 1)) * height;
    BB_RECT rect;

    Log_info("display_show_msg2 start");

    // Load the image into the bb_epaper framebuffer
    if (image_buffer && *(uint16_t *)image_buffer == BB_BITMAP_MARKER)
    {
        // G5 compressed image
        BB_BITMAP *pBBB = (BB_BITMAP *)image_buffer;
        int x = (width - pBBB->width)/2;
        int y = (height - pBBB->height)/2; // center it
        if (x > 0 || y > 0) // only clear if the image is smaller than the display
        {
            bbep.fillScreen(BBEP_WHITE);
        }
        bbep.loadG5Image(image_buffer, x, y, BBEP_WHITE, BBEP_BLACK);
    }
    else
    {
#ifdef BB_EPAPER
        if (image_buffer) memcpy(bbep.getBuffer(), image_buffer+62, Imagesize); // uncompressed 1-bpp bitmap
#endif
    }

#if defined( PARALLEL_EPD )
    bbep.setFont(Inter_18);
#else
    bbep.setFont(nicoclean_8);
#endif
    bbep.setTextColor(BBEP_BLACK, BBEP_WHITE);
    switch (message_type)
    {
    case FRIENDLY_ID:
    {
        Log_info("friendly id case");
        const char string1[] = "Please visit trmnl.com/start";
        bbep.getStringBox(string1, &rect);
#ifdef __BB_EPAPER__
        bbep.setCursor((bbep.width() - rect.w)/2, 400);
#else
        bbep.setCursor((bbep.width() - rect.w)/2, bbep.height() - 140 - rect.h*2);
#endif
        bbep.println(string1);

        String string2 = "with Friendly ID ";
        if (id)
        {
            string2 += friendly_id;
        }
        string2 += " to finish setup";
        bbep.getStringBox(string2, &rect);
        bbep.setCursor((bbep.width() - rect.w)/2, -1);
        bbep.print(string2);
    }
    break;
    case WIFI_CONNECT:
    {
        Log_info("wifi connect case");

        String string1 = "TRMNL firmware ";
        string1 += fw_version;
        bbep.setCursor(40, 48); // place in upper left corner
        bbep.println(string1);
        String string2 = "Connect your phone or computer to ";
        string2 += (message.length() > 0) ? "\"" + message + "\"" : String("the TRMNL");
        string2 += " Wi-Fi";
        bbep.getStringBox(string2, &rect);
#ifdef __BB_EPAPER__
        bbep.setCursor((bbep.width() - rect.w) / 2, 386);
#else
        bbep.setCursor((bbep.width() - rect.w) / 2, bbep.height() - 100 - rect.h);
#endif
        bbep.println(string2);
        const char string3[] = "or scan the QR code for help";
        bbep.getStringBox(string3, &rect);
        bbep.setCursor((bbep.width() - rect.w) / 2, -1);
        bbep.print(string3);
#ifdef __BB_EPAPER__
        bbep.loadG5Image(wifi_connect_qr, bbep.width() - 40 - 66, 40, BBEP_WHITE, BBEP_BLACK); // 66x66 QR code
#else // bigger for X
        bbep.loadG5Image(wifi_connect_qr, bbep.width() - (66*2) - 80, 80, BBEP_WHITE, BBEP_BLACK, 2.0f);
#endif
    }
    break;
    case MAC_NOT_REGISTERED:
    {
        UWORD y_start = 340;
        UWORD font_width = 18; // DEBUG
        Paint_DrawMultilineText(0, y_start, message.c_str(), width, font_width, BBEP_BLACK, BBEP_WHITE,
#if defined( BOARD_TRMNL_X ) || defined( BOARD_TRMNL_X_EPDIY ) || defined( BOARD_TRMNL_X_SENSORIAS3 ) || defined( BOARD_TRMNL_X_SENSORIAC5 ) || defined( BOARD_TRMNL_X_LILYGO ) || defined( BOARD_TRMNL_X_PAPERS3 )
        Inter_18, true);
#else
        nicoclean_8, true);
#endif
    }
    break;
    default:
        break;
    }
    Log_info("Start drawing...");
#ifdef BB_EPAPER
    if (!display_update_epaper(REFRESH_FULL, true, true, PLANE_0)) {
        Log_error("display_show_msg2: e-paper update failed");
        bbep.freeBuffer();
        return;
    }
    bbep.freeBuffer();
#else
    bbep.fullUpdate();
#endif
    Log_info("display_show_msg2 end");
}

/**
 * @brief Function to got the display to the sleep
 * @param none
 * @return none
 */
void display_sleep(void)
{
    Log_info("Goto Sleep...");
#ifdef BB_EPAPER
    bbep.sleep(LIGHT_SLEEP);
#else
    bbep.einkPower(0);
    bbep.deInit();
#ifdef BOARD_BRWR_TRMNL
    brwr::panel_release_lines(); // don't feed the unpowered HAT through its pins
#endif
#endif
}
