brewer-michael/brwr-trmnl/hardware/diagrams/wiring.py

"""wiring.svg: how the modules connect, seen from the back of the device.

All positions are front-view coordinates in mm (origin at the enclosure centre, +X right,
+Y up), taken from hardware/enclosure/brwr-trmnl.scad. The drawing is the view from the
back, so X is mirrored on screen.
"""

from __future__ import annotations

import math

import carrier as C
from svgkit import COL, Svg, text_w

W, H = 1400, 1100
K = 4.3                              # px per mm
CX, CY = 40 + 114.5 * K, 118 + 102 * K

# Enclosure and module geometry (front view, mm) -----------------------------------
OUT_W, OUT_H, WALL = 229.0, 204.0, 2.5
PANEL = (-108.35, -78.0, 108.35, 96.41)               # x0, y0, x1, y1
CAR_TOP = (OUT_H - 2 * WALL) / 2                       # 99.5: carrier top edge against the top wall
CARRIER = (-35.0, CAR_TOP - 35.0, 35.0, CAR_TOP)
HAT = (-73 - 32.5, -28.25, -73 + 32.5, 28.25)
HAT_PADS = (-47.5, 7.0, 21.0)                          # X, Y range: where the kit cable's wires are soldered (clear of the hole at -44, 24.75)
BATT = (56 - 50, -30.0, 56 + 50, 30.0)
FLEX = (-70.5, -78.0, 70.5, -60.0)                     # folded flex behind the panel
FLEX_ZONE = (-72.0, -78.0, 72.0, -38.0)
ADAPTER = (-25 - 15, -69.0, -25 + 15, -54.0)
FFC_X = -18.0                                          # 40-pin FFC leaves the adapter here, then turns to the HAT
STRIP = (-42.0, -99.0, 42.0, -79.0)                    # button board, 84 x 20, centre (0, -89)
BTN_X = {"BACK": -25.4, "REFRESH": 0.0, "NEXT": 25.4}
STRIP_SCREW_X = 36.83                                  # the strip's M2.5 holes, 14.5 pitches either side
MAGNETS = [(-90, 65), (90, 65), (-90, -65), (90, -65)]
MAG_D = 20.0                                           # N52 disc, sealed in the back cover
ANT = (38.0, 83.0)                                     # Taoglas FXP831 (45 x 7 mm), on a fin on the back cover
ANT_FIN_Y = (97.3, 98.5)                               # the fin, just inside the top wall; the antenna is on its inner face
RIB_Y, RIB_X = 36.0, 105.0                             # the interior rib the cables cross (up to the panel's foam)
RIB_GAPS = [(-41.5, -25.0), (1.0, 13.0)]               # its gaps: wire passage (and the back seam), battery lead
COAX_VIA = [(36.0, 90.0), (5.0, 82.0)]                 # where the coax runs over the carrier (builder's choice)
WIRE_X = -30.0                                         # button wires run up the back cover here (clear of its joint at -39)
TIES_Y = (-25.0, 15.0, 52.0)                           # zip-tie blocks on the back cover, 8 x 5 mm, at X = WIRE_X
PLUG = (-55.5, -61.0, -44.5, -45.0)                    # the button lead's inline JST-PH pair (J4), flat on the back cover
# Steel rods, 3 mm, epoxied: two straight across the back cover, four L-rods in the frame's corners
ROD_D = 3.0
ROD_BACK_Y, ROD_BACK_X = (45.5, -35.3), 103.0
ROD_CC, ROD_R = (108.5, 96.0), 3.3                     # bend centre (+X +Y corner) and centreline radius
ROD_LEGS = {(-1, 1): (40.0, 40.0), (1, 1): (15.5, 40.0), (-1, -1): (40.0, 48.0), (1, -1): (40.0, 48.0)}


def B(x, y):
    """Front-view mm -> back-view px (X mirrored)."""
    return CX - x * K, CY - y * K


def brect(s: Svg, r, **kw):
    x0, y0, x1, y1 = r
    (ax, ay), (bx, by) = B(x1, y1), B(x0, y0)
    s.rect(ax, ay, bx - ax, by - ay, **kw)
    return ax, ay, bx - ax, by - ay


def car(xc, yc):
    """Carrier-layout coordinates (component side, mm from the board centre / top edge) -> front mm."""
    return xc, CAR_TOP - yc


def smooth(pts):
    """Catmull-Rom through px points -> SVG path d."""
    d = f"M {pts[0][0]:.1f} {pts[0][1]:.1f}"
    for i in range(len(pts) - 1):
        p0 = pts[i - 1] if i > 0 else pts[i]
        p1, p2 = pts[i], pts[i + 1]
        p3 = pts[i + 2] if i + 2 < len(pts) else p2
        c1 = (p1[0] + (p2[0] - p0[0]) / 6, p1[1] + (p2[1] - p0[1]) / 6)
        c2 = (p2[0] - (p3[0] - p1[0]) / 6, p2[1] - (p3[1] - p1[1]) / 6)
        d += f" C {c1[0]:.1f} {c1[1]:.1f} {c2[0]:.1f} {c2[1]:.1f} {p2[0]:.1f} {p2[1]:.1f}"
    return d


def offset(pts, dist):
    """Offset a px polyline sideways by dist (for drawing parallel wires in a bundle)."""
    out = []
    for i, (x, y) in enumerate(pts):
        a = pts[max(i - 1, 0)]
        b = pts[min(i + 1, len(pts) - 1)]
        dx, dy = b[0] - a[0], b[1] - a[1]
        n = math.hypot(dx, dy) or 1
        out.append((x - dy / n * dist, y + dx / n * dist))
    return out


def bundle(s: Svg, pts, colors, gap=3.2, width=2.2, hidden_until=0, hidden_from=None):
    """Parallel coloured wires along a smooth path (px). A grey sleeve behind keeps them readable."""
    n = len(colors)
    s.path(smooth(pts), stroke="#ffffff", width=gap * n + 5)
    for i, c in enumerate(colors):
        o = (i - (n - 1) / 2) * gap
        s.path(smooth(offset(pts, o)), stroke=c, width=width)


def hatch_defs(s: Svg):
    s.defs.append('<pattern id="hatch" width="6" height="6" patternUnits="userSpaceOnUse" '
                  'patternTransform="rotate(45)"><rect width="6" height="6" fill="#eceff1"/>'
                  '<line x1="0" y1="0" x2="0" y2="6" stroke="#546e7a" stroke-width="1.6"/></pattern>')
    s.defs.append('<pattern id="flexfill" width="8" height="8" patternUnits="userSpaceOnUse">'
                  '<rect width="8" height="8" fill="#f3c16b"/>'
                  '<line x1="0" y1="0" x2="8" y2="0" stroke="#e0a73d" stroke-width="1"/></pattern>')


def label(s: Svg, x, y, rows, anchor="middle", size=12.5, box=True, bold_first=True):
    """Multi-line label with an optional white box behind it (px coordinates, y = first baseline)."""
    lh = size + 4
    w = max(text_w(r, size, bold_first and i == 0) for i, r in enumerate(rows)) + 12
    h = lh * len(rows) + 6
    x0 = x - w / 2 if anchor == "middle" else (x - 6 if anchor == "start" else x - w + 6)
    if box:
        s.rect(x0, y - size - 3, w, h, fill="#ffffff", stroke="#90a4ae", width=1, rx=4, opacity=0.95)
    for i, r in enumerate(rows):
        s.text(x0 + w / 2, y + i * lh, r, size=size, anchor="middle",
               weight="bold" if (bold_first and i == 0) else "normal",
               fill=COL["text"] if i == 0 else COL["text2"])
    return x0, y - size - 3, w, h


def rod(s: Svg, pts_mm):
    """3 mm steel rod along a front-view polyline (mm)."""
    d = "M " + " L ".join(f"{x:.1f} {y:.1f}" for x, y in (B(*p) for p in pts_mm))
    s.path(d, stroke="#546e7a", width=ROD_D * K + 1.6)
    s.path(d, stroke="#b0bec5", width=ROD_D * K - 1.6)
    s.path(d, stroke="#eceff1", width=1.6)


def rod_swatch(sv: Svg, cx, cy):
    sv.line(cx + 2, cy, cx + 34, cy, stroke="#546e7a", width=ROD_D * K + 1.6)
    sv.line(cx + 2, cy, cx + 34, cy, stroke="#b0bec5", width=ROD_D * K - 1.6)
    sv.line(cx + 2, cy, cx + 34, cy, stroke="#eceff1", width=1.6)


def rib_swatch(sv: Svg, cx, cy):
    sv.line(cx + 2, cy, cx + 14, cy, stroke="#78909c", width=1.6 * K)
    sv.line(cx + 22, cy, cx + 34, cy, stroke="#78909c", width=1.6 * K)


def tie_swatch(sv: Svg, cx, cy):
    sv.rect(cx + 1, cy - 10.5, 34, 21, fill="#cfd8dc", stroke="#546e7a", width=1.2, rx=2)
    for i, c in enumerate((COL["btn"], COL["gnd"])):
        sv.line(cx + 12 + i * 12, cy - 10.5, cx + 12 + i * 12, cy + 10.5, stroke=c, width=2.2)
    sv.rect(cx + 3, cy - 3, 30, 6, fill="#263238", stroke="none", width=0, rx=2)


def ffc_swatch(sv: Svg, cx, cy):
    sv.line(cx, cy, cx + 36, cy, stroke="#9e9e9e", width=9, stroke_linecap="butt")
    sv.line(cx, cy, cx + 36, cy, stroke="#fbfbfb", width=7, stroke_linecap="butt")


# ------------------------------------------------------------------------------ drawing
def draw_enclosure(s: Svg):
    r = (-OUT_W / 2, -OUT_H / 2, OUT_W / 2, OUT_H / 2)
    brect(s, r, fill="#cfd4da", stroke="#37474f", width=2, rx=5 * K)
    brect(s, (r[0] + WALL, r[1] + WALL, r[2] - WALL, r[3] - WALL), fill="#eef0f3", stroke="#90a4ae", width=1,
          rx=3 * K)
    brect(s, PANEL, fill="#dde1e6", stroke="#9aa5b1", width=1.2)
    # magnet keep-out rule: 36 mm from the magnet centre to any board edge (clipped to the interior)
    ax, ay = B(OUT_W / 2 - WALL, OUT_H / 2 - WALL)
    s.defs.append(f'<clipPath id="inside"><rect x="{ax:.1f}" y="{ay:.1f}" width="{(OUT_W - 2 * WALL) * K:.1f}" '
                  f'height="{(OUT_H - 2 * WALL) * K:.1f}"/></clipPath>')
    circles = "".join(f'<circle cx="{B(mx, my)[0]:.1f}" cy="{B(mx, my)[1]:.1f}" r="{36 * K:.1f}" fill="none" '
                      f'stroke="#e57373" stroke-width="1.1" stroke-dasharray="5 4"/>' for mx, my in MAGNETS)
    s.add(f'<g clip-path="url(#inside)">{circles}</g>')


def draw_flex(s: Svg):
    brect(s, FLEX_ZONE, fill="none", stroke="#c28a2c", width=1, stroke_dasharray="6 4")
    brect(s, FLEX, fill="url(#flexfill)", stroke="#b7791f", width=1.2)
    x, y, w, h = brect(s, ADAPTER, fill="#2f6b4f", stroke="#1b4332", width=1.4, rx=3)
    s.text(x + 8, y + h / 2 + 4.5, "adapter", size=12, anchor="start", fill="#ffffff", weight="bold")  # clear of the button lead


def draw_battery(s: Svg):
    x, y, w, h = brect(s, BATT, fill="#4f5b66", stroke="#263238", width=1.6, rx=6)
    s.text(x + w / 2, y + h / 2 - 8, "BT1  LiPo 3.7 V  5000 mAh", size=14, anchor="middle", weight="bold",
           fill="#ffffff")
    s.text(x + w / 2, y + h / 2 + 12, "100 × 60 × 6 mm, in its cradle", size=12.5, anchor="middle", fill="#e0e0e0")


def draw_hat(s: Svg):
    x, y, w, h = brect(s, HAT, fill="#2f6b4f", stroke="#1b4332", width=1.6, rx=4)
    # the Pi header is cut off: its 2 x 20 clipped pins stay along the +Y edge (facing you)
    hx0, hy0 = -73 - 25.4, 28.25 - 3.5 - 2.55
    for i in range(20):
        for j in range(2):
            cx, cy = B(hx0 + 1.27 + 2.54 * i, hy0 + 1.27 + 2.54 * j)
            s.circle(cx, cy, 2.0, fill="#c5ccd3", stroke="none", width=0)
    for sx_, sy_ in [(-73 + a * 29, b * 24.75) for a in (-1, 1) for b in (-1, 1)]:
        cx, cy = B(sx_, sy_)
        s.circle(cx, cy, 2.3 * K, fill="#90a4ae", stroke="#37474f", width=1.2)     # countersunk screw heads
        s.circle(cx, cy, 0.9, fill="#37474f", stroke="none", width=0)
    # FFC socket on the +X edge (panel side, drawn dashed)
    brect(s, (-40.5 - 5, -15, -40.5, 15), fill="none", stroke="#ffffff", width=1.4, stroke_dasharray="4 3")
    # the 8 pads the kit cable's wires are soldered to, where its 8-pin socket was (panel side)
    px_, y0, y1 = HAT_PADS
    for i in range(8):
        cx, cy = B(px_, y0 + (y1 - y0) * i / 7)
        s.rect(cx - 3.4, cy - 3.4, 6.8, 6.8, fill="none", stroke="#ffffff", width=1.1, stroke_dasharray="2 1.5")
    s.text(x + w / 2 + 14, y + h / 2 - 2, "U2  driver HAT", size=14, anchor="middle", weight="bold", fill="#ffffff")
    s.text(x + w / 2 + 14, y + h / 2 + 17, "IT8951, DIP switches: SPI", size=12, anchor="middle", fill="#e8f5e9")
    s.text(x + w / 2 + 14, y + h / 2 + 34, "Pi header cut off, pins clipped", size=12, anchor="middle",
           fill="#e8f5e9")


def draw_carrier(s: Svg):
    """Carrier seen from its solder side: board, holes, and the parts on the far side dashed."""
    brect(s, CARRIER, fill="#efe2c4", stroke="#8d7b5a", width=1.4, rx=2)
    for k in range(27):
        for r in range(13):
            cx, cy = B(*car(C.hx(k), C.hy(r)))
            s.circle(cx, cy, 1.5, fill="#c9ab76", stroke="none", width=0)
    for mx, my in C.MOUNT:                     # countersunk M2.5 screws from the back, nuts on the far side
        cx, cy = B(*car(mx, my))
        s.circle(cx, cy, 2.35 * K, fill="#90a4ae", stroke="#37474f", width=1.2)
        s.circle(cx, cy, 0.9, fill="#37474f", stroke="none", width=0)
    # far-side parts (component side faces the panel)
    far = dict(fill="#ffffff", stroke="#546e7a", width=1.2, stroke_dasharray="4 3", opacity=0.9)
    for part, name in ((C.U4, "U4 charger"), (C.XIAO, "U1 XIAO"), (C.U3, "U3")):
        xa, ya = car(part["x0"], part["y0"])
        xb, yb = car(part["x0"] + part["w"], part["y0"] + part["h"])
        bx, by, bw, bh = brect(s, (xa, yb, xb, ya), **far)
        ly = by + 48 if name == "U1 XIAO" else by + bh - 10
        s.text(bx + bw / 2, ly, name, size=11.5, anchor="middle", weight="bold", fill="#37474f")
    # USB-C connectors overhang the top edge
    for ux in (-7.62, 22.0):
        brect(s, (ux - 4.47, CAR_TOP - 5.8, ux + 4.47, CAR_TOP + 1.5), fill="#b0bec5", stroke="#546e7a", width=1.2,
              rx=4)
    # J2, J3, J1: the holes their wires are soldered into
    for k, r0, n in ((15, 2, 8), (5, 0, 4)):
        for i in range(n):
            cx, cy = B(*car(C.hx(k), C.hy(r0 + i)))
            s.circle(cx, cy, 2.8, fill="#d4af37", stroke="#6d5b1f", width=0.9)
    for k in (20, 21):
        cx, cy = B(*car(C.hx(k), C.hy(11)))
        s.circle(cx, cy, 2.8, fill="#d4af37", stroke="#6d5b1f", width=0.9)


def draw_strip(s: Svg):
    x, y, w, h = brect(s, STRIP, fill="#efe2c4", stroke="#8d7b5a", width=1.4, rx=2)
    for bx in (-STRIP_SCREW_X, STRIP_SCREW_X):
        cx, cy = B(bx, -89.0)
        s.circle(cx, cy, 1.35 * K, fill="#ffffff", stroke="#616161", width=1.2)
    for name, bx in BTN_X.items():
        brect(s, (bx - 6, -95, bx + 6, -83), fill="#ffffff", stroke="#546e7a", width=1.2, stroke_dasharray="4 3")
        cx, cy = B(bx, -89.0)
        s.circle(cx, cy, 3.2 * K, fill="none", stroke="#90a4ae", width=1, stroke_dasharray="3 3")
        s.text(cx, cy + 4, name, size=11.5, anchor="middle", weight="bold", fill="#1b5e20")


def draw_antenna(s: Svg):
    brect(s, (ANT[0], ANT_FIN_Y[0], ANT[1], ANT_FIN_Y[1]), fill="#b0bec5", stroke="#546e7a", width=1)       # fin
    brect(s, (ANT[0], ANT_FIN_Y[0] - 1.4, ANT[1], ANT_FIN_Y[0]), fill="#c9a227", stroke="#8d6e1f", width=1.2)
    return (ANT[0] + 3, ANT_FIN_Y[0] - 0.7)


def draw_rib(s: Svg):
    """The interior rib at Y = 36: solid up to the panel's foam, so cables cross only at its gaps."""
    xs = [-RIB_X] + [x for g in RIB_GAPS for x in g] + [RIB_X]
    for a, b in zip(xs[0::2], xs[1::2]):
        (ax, ay), (bx, by) = B(a, RIB_Y), B(b, RIB_Y)
        s.line(ax, ay, bx, by, stroke="#78909c", width=1.6 * K, stroke_linecap="butt")


def draw_rods(s: Svg):
    for y in ROD_BACK_Y:                                       # in channels on the back cover
        rod(s, [(-ROD_BACK_X, y), (ROD_BACK_X, y)])
    cx0, cy0 = ROD_CC
    for (sx, sy), (l_top, l_side) in ROD_LEGS.items():        # in grooves in the frame's corners
        side = [(sx * (cx0 + ROD_R), sy * (cy0 - l_side)), (sx * (cx0 + ROD_R), sy * cy0)]
        arc = [(sx * (cx0 + ROD_R * math.cos(math.radians(a))), sy * (cy0 + ROD_R * math.sin(math.radians(a))))
               for a in range(15, 90, 15)]
        top = [(sx * cx0, sy * (cy0 + ROD_R)), (sx * (cx0 - l_top), sy * (cy0 + ROD_R))]
        rod(s, side + arc + top)


def draw_ties(s: Svg):
    for y in TIES_Y:
        brect(s, (WIRE_X - 4, y - 2.5, WIRE_X + 4, y + 2.5), fill="#cfd8dc", stroke="#546e7a", width=1.2, rx=2)


def draw_cables(s: Svg, feed):
    P = lambda pts: [B(x, y) for x, y in pts]
    # 40-pin FFC: adapter -> HAT socket on its +X edge (near the panel; the button lead crosses it once)
    fx0, fy0 = B(FFC_X, -54)
    fx1, fy1 = B(FFC_X, -16)
    fx2, fy2 = B(-40.5, 0)
    d = (f"M {fx0:.1f} {fy0:.1f} L {fx1:.1f} {fy1:.1f} "
         f"Q {fx1:.1f} {fy2:.1f} {fx2:.1f} {fy2:.1f}")
    for col, wd in (("#9e9e9e", 11 * K + 3), ("#fbfbfb", 11 * K)):
        s.add(f'<path d="{d}" fill="none" stroke="{col}" stroke-width="{wd:.1f}" stroke-linejoin="round"/>')
    s.path(d, stroke="#d6d6d6", width=1)
    # battery lead: cradle slot on the -X wall (front) -> JST-PH plug -> J1's pigtail -> the carrier
    jx = (C.hx(20) + C.hx(21)) / 2
    bat = P([(6.5, 2), (4.2, 20), (5.2, 31), (6.5, 36), (10, 44), (15.5, 55), (jx, 61), (jx, CAR_TOP - 35.4)])
    bundle(s, bat, [COL["gnd"], COL["vbat"]], gap=3.4, width=2.6)
    for (xe, k), col in (((jx + 0.4, 20), COL["gnd"]), ((jx - 0.4, 21), COL["vbat"])):   # pigtail on the far side
        a, b = B(xe, CAR_TOP - 35.4), B(*car(C.hx(k), C.hy(11)))
        s.path(f"M {a[0]:.1f} {a[1]:.1f} L {b[0]:.1f} {b[1]:.1f}", stroke=col, width=2.2, stroke_dasharray="4 3")
    x, y, w, h = brect(s, (6.5 - 3.2, 36 - 2.4, 6.5 + 3.2, 36 + 2.4), fill="#f5f0e1", stroke="#8d8672", width=1.3,
                       rx=2)
    s.text(x + w + 6, y + h / 2 + 4, "JST-PH", size=11.5, weight="bold", fill=COL["text2"])
    # button lead: strip -> its inline JST-PH pair (J4), flat on the back cover beside the adapter -> up the
    # back cover at X = -30, tied to three blocks -> through the tray's wire gap -> over the carrier's parts
    # (far side) to J3
    plug_x = (PLUG[0] + PLUG[2]) / 2
    btn_cols = [COL["btn"], COL["btn"], COL["btn"], COL["gnd"]]
    bundle(s, P([(WIRE_X, -79), (-33.5, -74.5), (-45.5, -68), (plug_x, -64), (plug_x, PLUG[1])]), btn_cols)
    btn_vis = P([(plug_x, PLUG[3]), (plug_x, -41.5), (-44, -36.5), (-33, -30), (WIRE_X, TIES_Y[0]),
                 (WIRE_X, TIES_Y[1]), (WIRE_X, TIES_Y[2]), (-29.4, 60.5), (-26.8, CAR_TOP - 35.4)])
    bundle(s, btn_vis, btn_cols)
    x, y, w, h = brect(s, PLUG, fill="#f5f0e1", stroke="#8d8672", width=1.3, rx=2)
    s.line(x, y + h / 2, x + w, y + h / 2, stroke="#8d8672", width=1.3)          # where the two halves mate
    s.text(x + w + 6, y + h / 2 - 3, "J4", size=12, weight="bold")
    s.text(x + w + 6, y + h / 2 + 13, "JST-PH", size=11.5, weight="bold", fill=COL["text2"])
    for y in TIES_Y:                                           # zip ties round the wires
        brect(s, (WIRE_X - 3.6, y - 1.25, WIRE_X + 3.6, y + 1.25), fill="#263238", stroke="none", width=0, rx=2)
    btn_hid = P([(-26.8, CAR_TOP - 35.4), (-22.4, CAR_TOP - 31.2), (-22.4, CAR_TOP - 13.4), car(C.hx(5), C.hy(3))])
    s.path(smooth(btn_hid), stroke=COL["btn"], width=2.4, stroke_dasharray="5 4")
    # HAT wires (the kit cable, plug cut off): J2 -> over the carrier's parts -> round the HAT's top edge to its pads
    j2 = car(C.hx(15), C.hy(9))
    hat_hid = P([j2, (C.hx(15), CAR_TOP - 35.4)])
    s.path(smooth(hat_hid), stroke=COL["spi"], width=2.4, stroke_dasharray="5 4")
    hat_vis = P([(C.hx(15), CAR_TOP - 35.4), (3.5, 56), (-10, 46.5), (-26, 40.5), (-35, 36), (-42, 32.5),
                 (HAT_PADS[0], 29.6)])   # through the rib's wire gap, left of the button lead
    bundle(s, hat_vis, [COL["v5"], COL["gnd"], COL["spi"], COL["spi"], COL["spi"], COL["spi"], COL["ctl"],
                        COL["ctl"]], gap=2.6, width=1.9)
    a, b = B(HAT_PADS[0], 29.6), B(HAT_PADS[0], (HAT_PADS[1] + HAT_PADS[2]) / 2)
    s.path(f"M {a[0]:.1f} {a[1]:.1f} L {b[0]:.1f} {b[1]:.1f}", stroke=COL["spi"], width=2.4, stroke_dasharray="5 4")
    # antenna coax (FXP831, 100 mm): feed at the antenna's -X end (front) -> over the carrier (hidden) -> U.FL
    ufl = car(*C.UFL)
    coax = P([feed, (38.6, 94.2), COAX_VIA[0]])
    s.path(smooth(coax), stroke=COL["coax"], width=2.6, stroke_dasharray="6 4")
    coax_h = P([COAX_VIA[0], COAX_VIA[1], ufl])
    s.path(smooth(coax_h), stroke=COL["coax"], width=2.2, stroke_dasharray="3 4")
    cx, cy = B(*ufl)
    s.circle(cx, cy, 3.4, fill="#c9a227", stroke="#6d5b1f", width=1)


def draw_magnets(s: Svg):
    r = MAG_D / 2
    for mx, my in MAGNETS:
        cx, cy = B(mx, my)
        s.circle(cx, cy, r * K, fill="url(#hatch)", stroke="#37474f", width=1.6)
    # the nearest board to a magnet edge: the HAT, 26.75 mm below the upper-right magnet (back view)
    x, y_top = B(-90, 65 - r)
    _, y_hat = B(-90, 28.25)
    s.line(x, y_top, x, y_hat, stroke="#c62828", width=1.4)
    for yy, sgn in ((y_top, 1), (y_hat, -1)):
        s.polygon([(x, yy), (x - 4, yy + 8 * sgn), (x + 4, yy + 8 * sgn)], fill="#c62828", stroke="none", width=0)
        s.line(x - 12, yy, x + 12, yy, stroke="#c62828", width=1)
    return x


def build() -> str:
    s = Svg(W, H, "brwr-trmnl v1 wiring, back view",
            "Where each module sits and how the cables run, seen from the back through the back cover: carrier, "
            "driver HAT, battery, panel flex and adapter, button board, antenna, magnets, steel rods, tie blocks and "
            "the rib the cables cross.")
    hatch_defs(s)
    s.text(40, 40, "brwr-trmnl v1 — wiring, seen from the back", size=22, weight="bold")
    s.text(40, 66, "Seen from the back through the back cover's plate (its rods, magnets, tie blocks and one rib are "
                   "drawn). Left and right are swapped", size=13.5, fill=COL["text2"])
    s.text(40, 86, "compared with the front: the HAT is on the right here. Dashed outlines are parts on the far side "
                   "of a board, facing the panel. Positions from the enclosure model.", size=13.5, fill=COL["text2"])

    draw_enclosure(s)
    draw_flex(s)
    draw_battery(s)
    draw_hat(s)
    draw_carrier(s)
    draw_strip(s)
    feed = draw_antenna(s)
    draw_rods(s)
    draw_rib(s)
    draw_ties(s)
    draw_cables(s, feed)
    dim_x = draw_magnets(s)
    annotate(s, dim_x)
    return s.render()


def num(s: Svg, x, y, n, r=10):
    s.circle(x, y, r, fill="#ffffff", stroke="#37474f", width=1.6)
    s.text(x, y + 4.5, str(n), size=12.5, anchor="middle", weight="bold")


def annotate(s: Svg, dim_x):
    # top edge: antenna and USB-C slots
    y = 108
    s.text(B(sum(ANT) / 2, 0)[0], y, "ANT1 FXP831 on its fin", size=12, anchor="middle", weight="bold")
    s.text(B(22, 0)[0], y, "USB-C charging", size=12, anchor="middle", weight="bold")
    s.text(B(-7.62, 0)[0], y, "USB-C flash, logs", size=12, anchor="middle", weight="bold")

    # carrier tags and label
    def tag(x, y, t):
        w = text_w(t, 12, True) + 10
        s.rect(x - w / 2, y - 10, w, 20, fill="#ffffff", stroke="#455a64", width=1.1, rx=4)
        s.text(x, y + 4.3, t, size=12, anchor="middle", weight="bold")

    tag(B(C.hx(15), 0)[0], B(0, CAR_TOP - 6.4)[1] - 6, "J2")
    tag(B(C.hx(5), 0)[0], B(0, CAR_TOP - 16.2)[1], "J3")
    tag(B(21.59 - 10.2, 0)[0], B(0, CAR_TOP - 32.3)[1], "J1")
    label(s, 778, 154, ["Carrier", "solder side faces you;", "parts face the panel"], size=12)

    # cable numbers
    num(s, *B(-24, 36), 1)
    num(s, *B(15.5, 55), 2)
    num(s, *B(WIRE_X, -5), 3)
    num(s, *B(38.6, 94.2), 4)
    num(s, *B(FFC_X, -30), 5)

    # module labels
    label(s, 232, 934, ["Button board", "SW1–SW3 face the front"], size=12)
    s.text(B(40, 0)[0], B(0, -71)[1] + 4, "panel flex, folded behind the panel", size=12, anchor="middle",
           weight="bold", fill="#5d4037")
    s.text(B(40, 0)[0], B(0, -42)[1], "flex zone, 144 × 40 mm: no ribs or rods", size=11.5, anchor="middle",
           fill="#8d6e1f")
    for i, r in enumerate(("Back of the", "10.3″ panel")):     # between the lower back rod and the magnet
        s.text(B(91, 0)[0], B(0, -42.5)[1] + i * 17, r, size=12.5, anchor="middle", fill=COL["text2"], weight="bold")
    # the distance label sits between the lower back rod's neighbour (Y 45.5) and the HAT
    label(s, dim_x + 10, B(0, 40.6)[1] + 15.5, ["≥ 25 mm", "from any board"], anchor="start", size=12)
    label(s, B(90, 0)[0], B(0, -65 - 17)[1], ["Magnet Ø20 × 3 (4×)"], size=12)

    # ---- side panel
    x0 = 1045
    _, lh = s.legend(x0, 118, title="Colour code", col_w=320, size=12.5,
                     extra=[(ffc_swatch, "40-pin FFC (panel)"), (rod_swatch, "Steel rod, 3 mm, epoxied"),
                            (rib_swatch, "Rib: cables cross only at its gaps"),
                            (tie_swatch, "Tie block and zip tie")])
    y = 118 + lh + 14
    cables = [("Kit 8-wire cable, plug cut off:", "soldered to the HAT's SPI pads and J2"),
              ("JST-PH pigtail (J1) ← battery plug.", "Check the polarity with a meter first."),
              ("4-wire lead: button board → J4 → J3,", "a JST-PH pair inline; tied at X = −30"),
              ("FXP831 coax, 100 mm: antenna → U1,", "U.FL, over the carrier's parts"),
              ("40-pin FFC: adapter → HAT socket", "on the HAT's +X edge")]
    s.rect(x0, y, 344, 44 + len(cables) * 42, fill="#ffffff", stroke=COL["blockline"], width=1.2, rx=6)
    s.text(x0 + 12, y + 22, "Cables", size=13, weight="bold")
    for i, (a, b) in enumerate(cables):
        yy = y + 50 + i * 42
        num(s, x0 + 22, yy - 4, i + 1)
        s.text(x0 + 40, yy, a, size=12.5, weight="bold")
        s.text(x0 + 40, yy + 17, b, size=12.5, fill=COL["text2"])
    y = y + 44 + len(cables) * 42 + 14
    notes = ["Front-view X is mirrored here: the charger",
             "(X = +22) is left of the XIAO (X = −7.6), and the",
             "MiniBoost (X = −29) is at the carrier's right end.",
             "",
             "The antenna sticks to a fin on the back cover,",
             "so it and the XIAO stay connected when the",
             "case is opened; only the FFC and J4 cross.",
             "",
             "The carrier and HAT face the panel: their wires",
             "sit between board and panel. Route the cables",
             "round the board edges as drawn.",
             "",
             "Magnets: 20 × 3 mm N52, sealed in the back",
             "cover under a 0.6 mm skin, each with a 20 × 1.5",
             "mm steel disc epoxied on and a 1 mm rubber pad",
             "outside. ≥ 25 mm from any board edge (dashed",
             "circles: 36 mm from each centre).",
             "",
             "Enclosure 229 × 204 × 13 mm."]
    s.rect(x0, y, 344, 36 + len(notes) * 18, fill=COL["note"], stroke=COL["noteline"], width=1.2, rx=6)
    s.text(x0 + 12, y + 22, "Notes", size=13, weight="bold")
    for i, n in enumerate(notes):
        s.text(x0 + 12, y + 44 + i * 18, n, size=12.5)
